freeDSP/freeDSP-aurora/SOURCES/WEBAPP/ESP32/testing/dsp.html

Channel 1 | Input | HP | LShlv | PEQ | PEQ | PEQ | PEQ | PEQ | PEQ | PEQ | PEQ | PEQ | PEQ | HShlv | LP | Phase | Delay | Gain | OUT 1
Channel 2 | Input | HP | LShlv | PEQ | PEQ | PEQ | PEQ | PEQ | PEQ | PEQ | PEQ | PEQ | PEQ | HShlv | LP | Phase | Delay | Gain | OUT 2
Channel 3 | Input | HP | LShlv | PEQ | PEQ | PEQ | PEQ | PEQ | PEQ | PEQ | PEQ | PEQ | PEQ | HShlv | LP | Phase | Delay | Gain | OUT 3
Channel 4 | Input | HP | LShlv | PEQ | PEQ | PEQ | PEQ | PEQ | PEQ | PEQ | PEQ | PEQ | PEQ | HShlv | LP | Phase | Delay | Gain | OUT 4
Channel 5 | Input | HP | LShlv | PEQ | PEQ | PEQ | PEQ | PEQ | PEQ | PEQ | PEQ | PEQ | PEQ | HShlv | LP | Phase | Delay | Gain | OUT 5
Channel 6 | Input | HP | LShlv | PEQ | PEQ | PEQ | PEQ | PEQ | PEQ | PEQ | PEQ | PEQ | PEQ | HShlv | LP | Phase | Delay | Gain | OUT 6
Channel 7 | Input | HP | LShlv | PEQ | PEQ | PEQ | PEQ | PEQ | PEQ | PEQ | PEQ | PEQ | PEQ | HShlv | LP | Phase | Delay | Gain | OUT 7
Channel 8 | Input | HP | LShlv | PEQ | PEQ | PEQ | PEQ | PEQ | PEQ | PEQ | PEQ | PEQ | PEQ | HShlv | LP | Phase | Delay | Gain | OUT 8

×

Input

Send

×

High Pass
| Hz
Send

×

Low Shelving
| dB
| Hz
| S
Send

×

Parametric EQ
| dB
| Hz
| Q
Send

×

High Shelving
| dB
| Hz
| S
Send

×

Low Pass
| Hz
Send

×

Phase
| Hz
| Q
Invert
Send

×

Delay
| ms
Send

×

Gain
| dB
Send
