freeDSP/freeDSP-aurora/ADDONS/AddOnA 1.0.0/KICAD/AddOnA.pdf

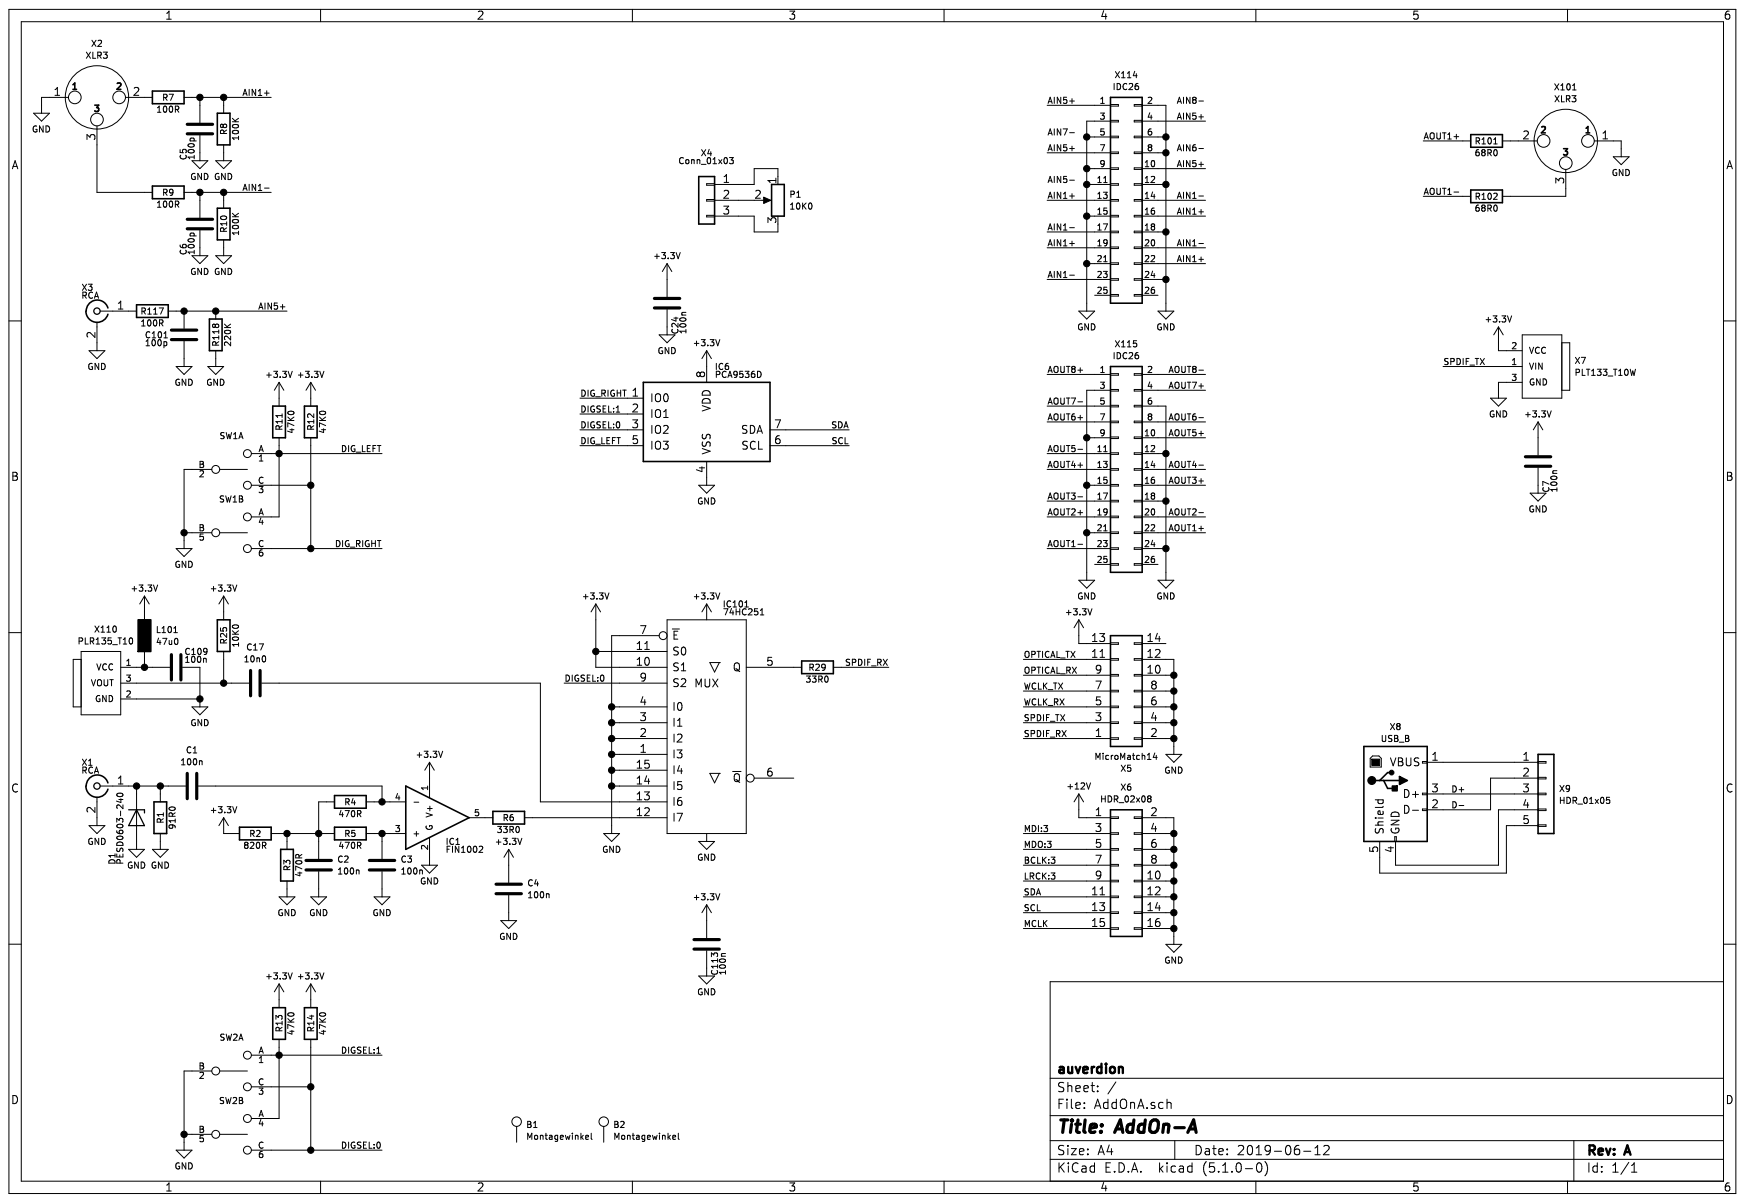
[picture p36: page 1]
