freeDSP/freeDSP-aurora/ADDONS/AddOnC/KICAD/AddOnC.pdf

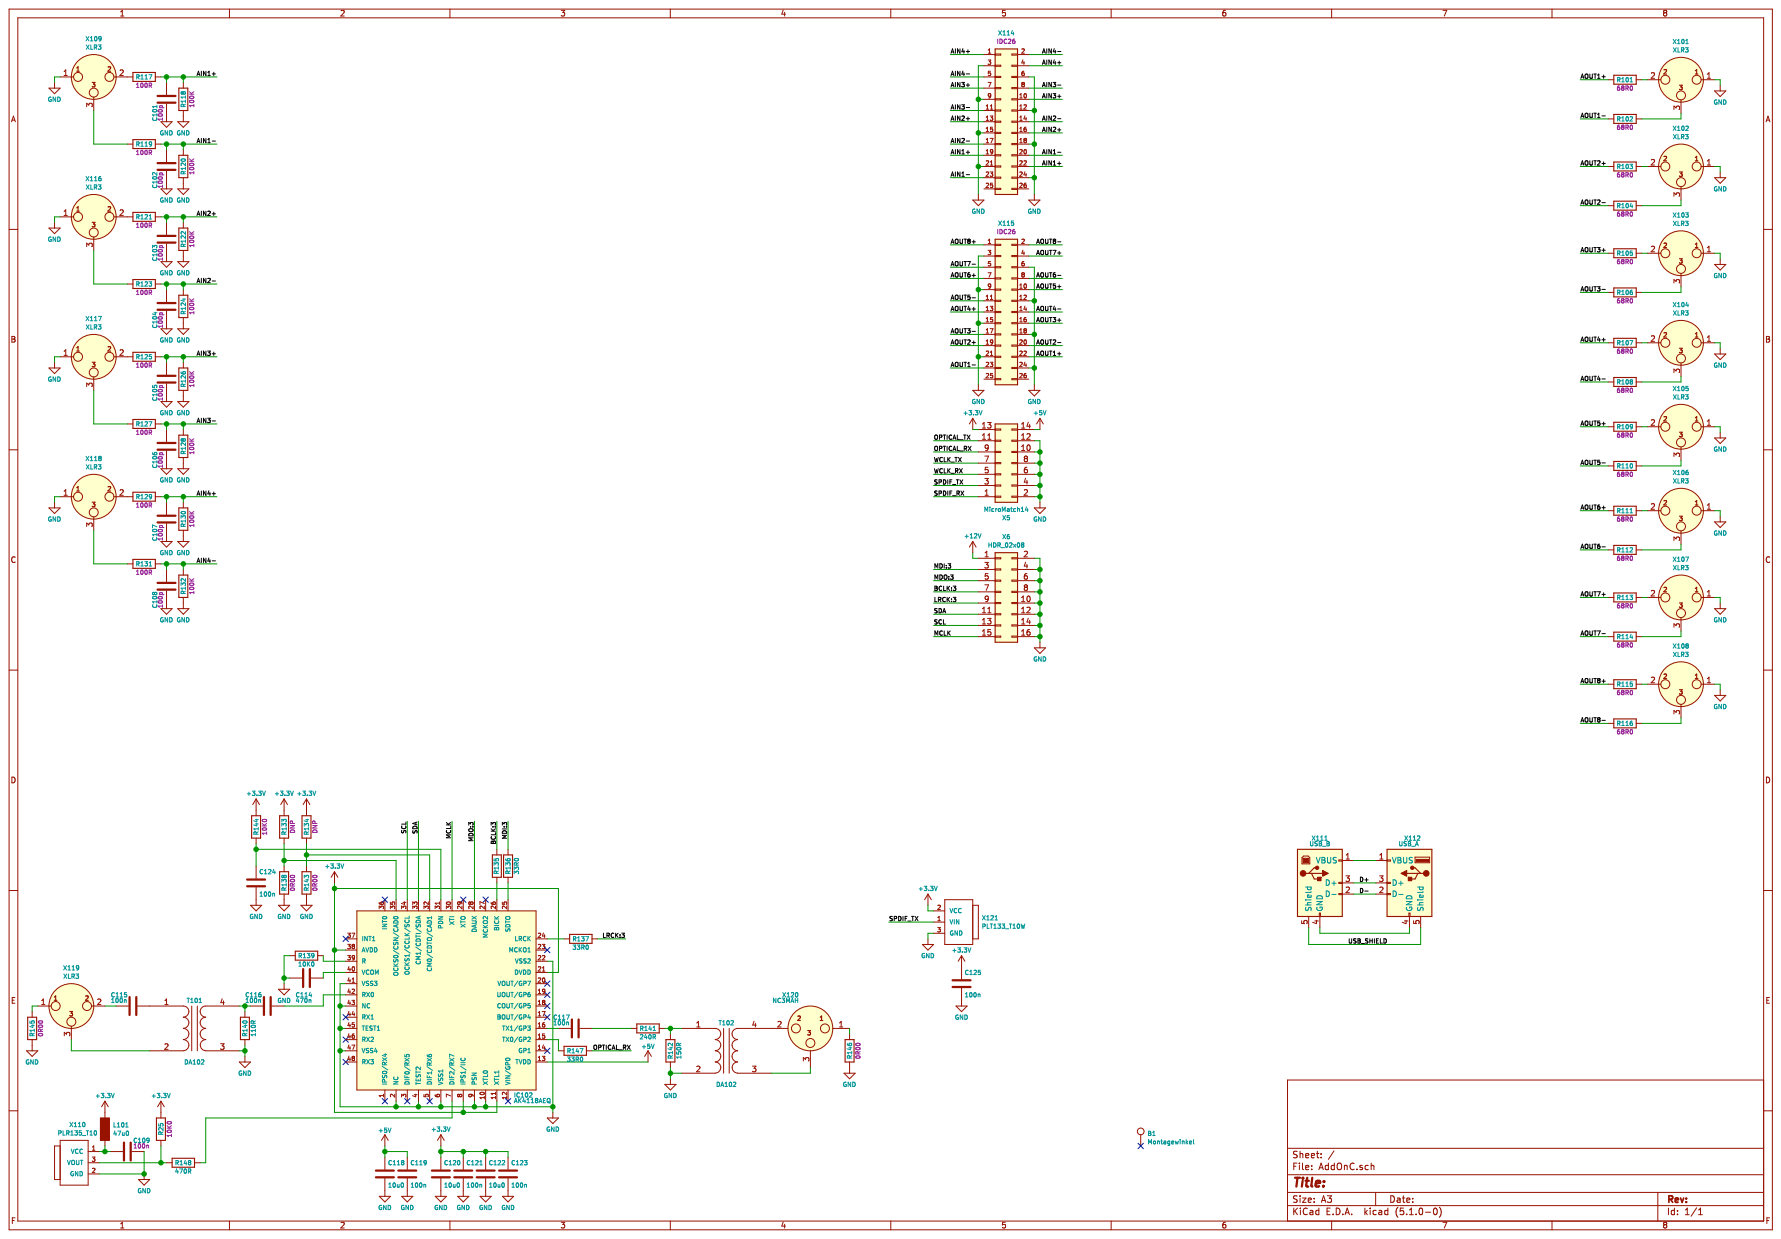
[picture p37: page 1]
