freeDSP/freeDSP-aurora/ADDONS/AddOnB/KICAD/Board A/AddOnB_BoardA.pdf

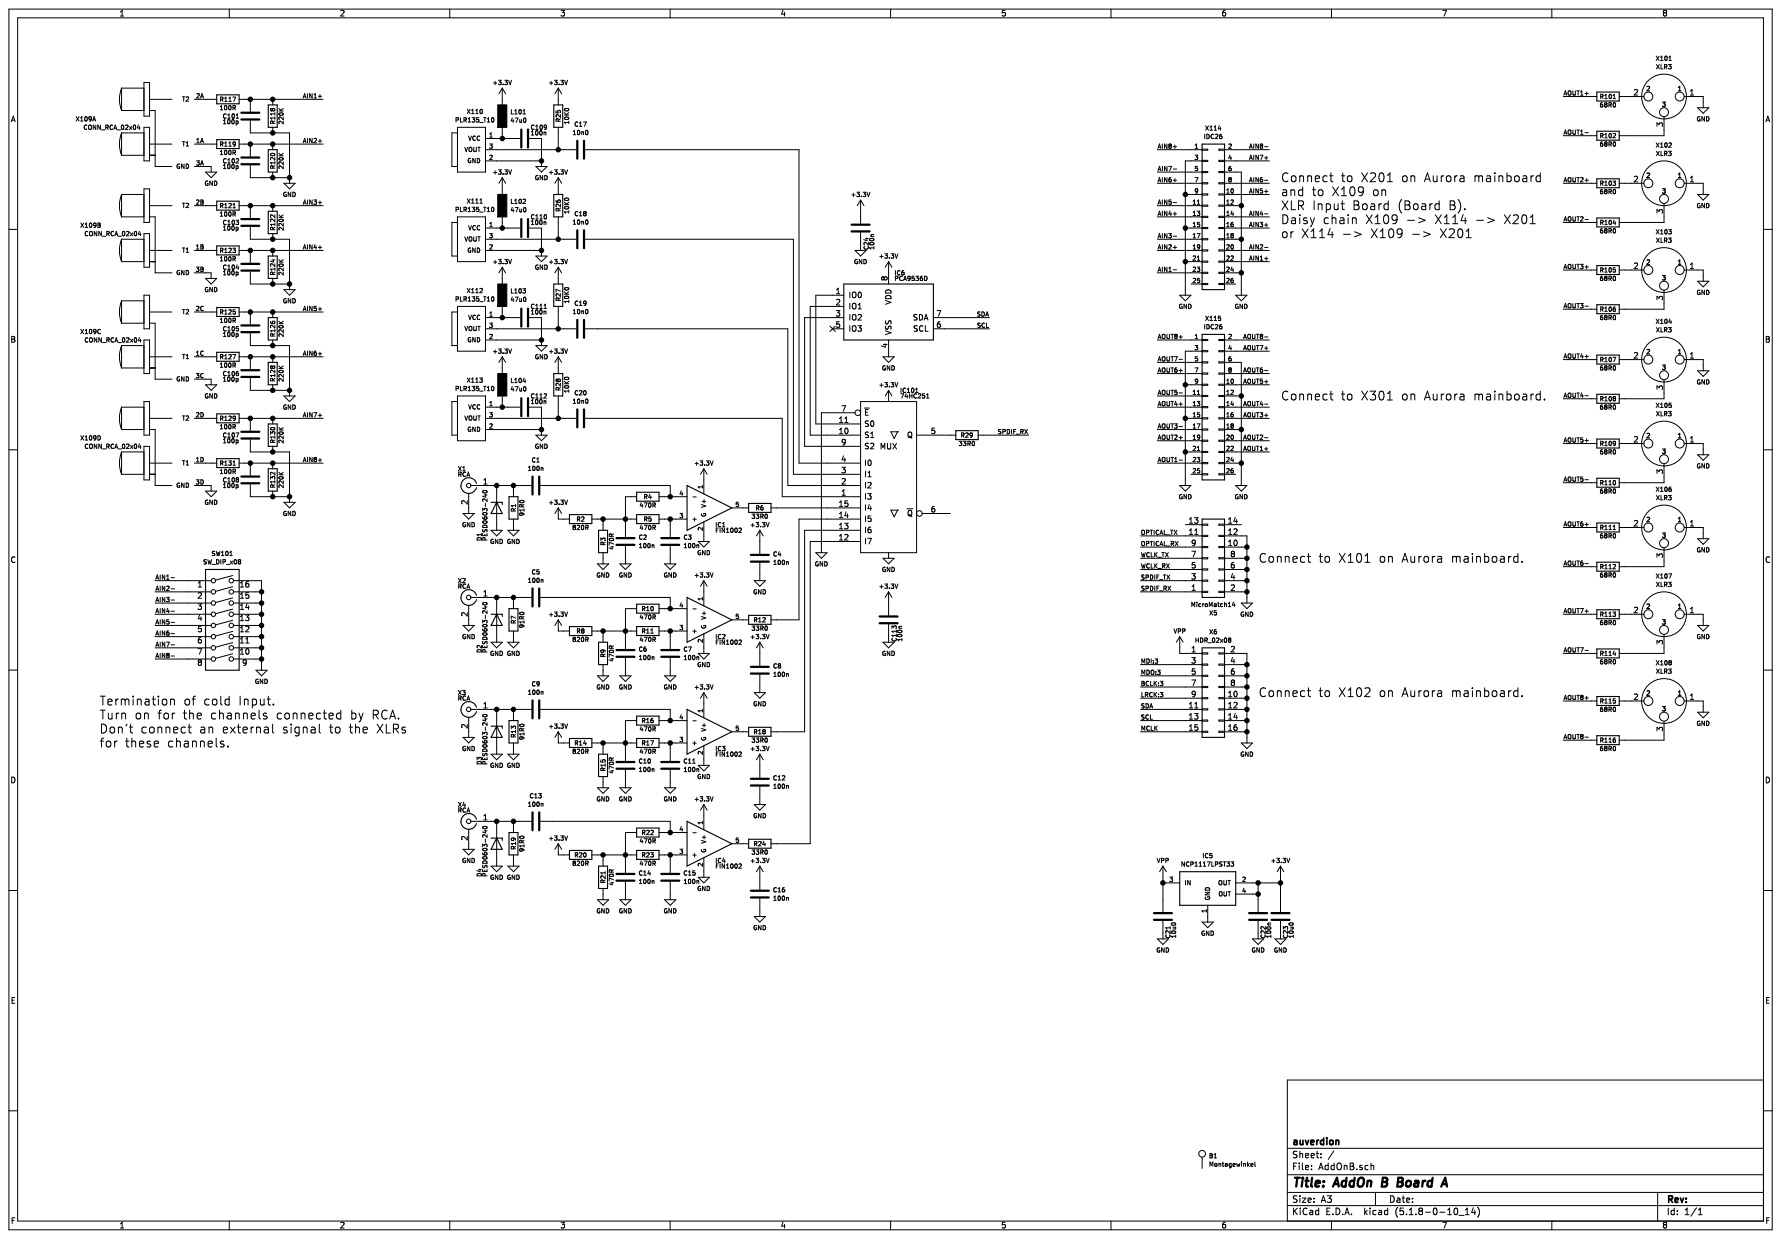
[picture p38: page 1]
