freeDSP/freeDSP-aurora/ADDONS/AddOnB/KICAD/Board B/AddOnB_BoardB.pdf

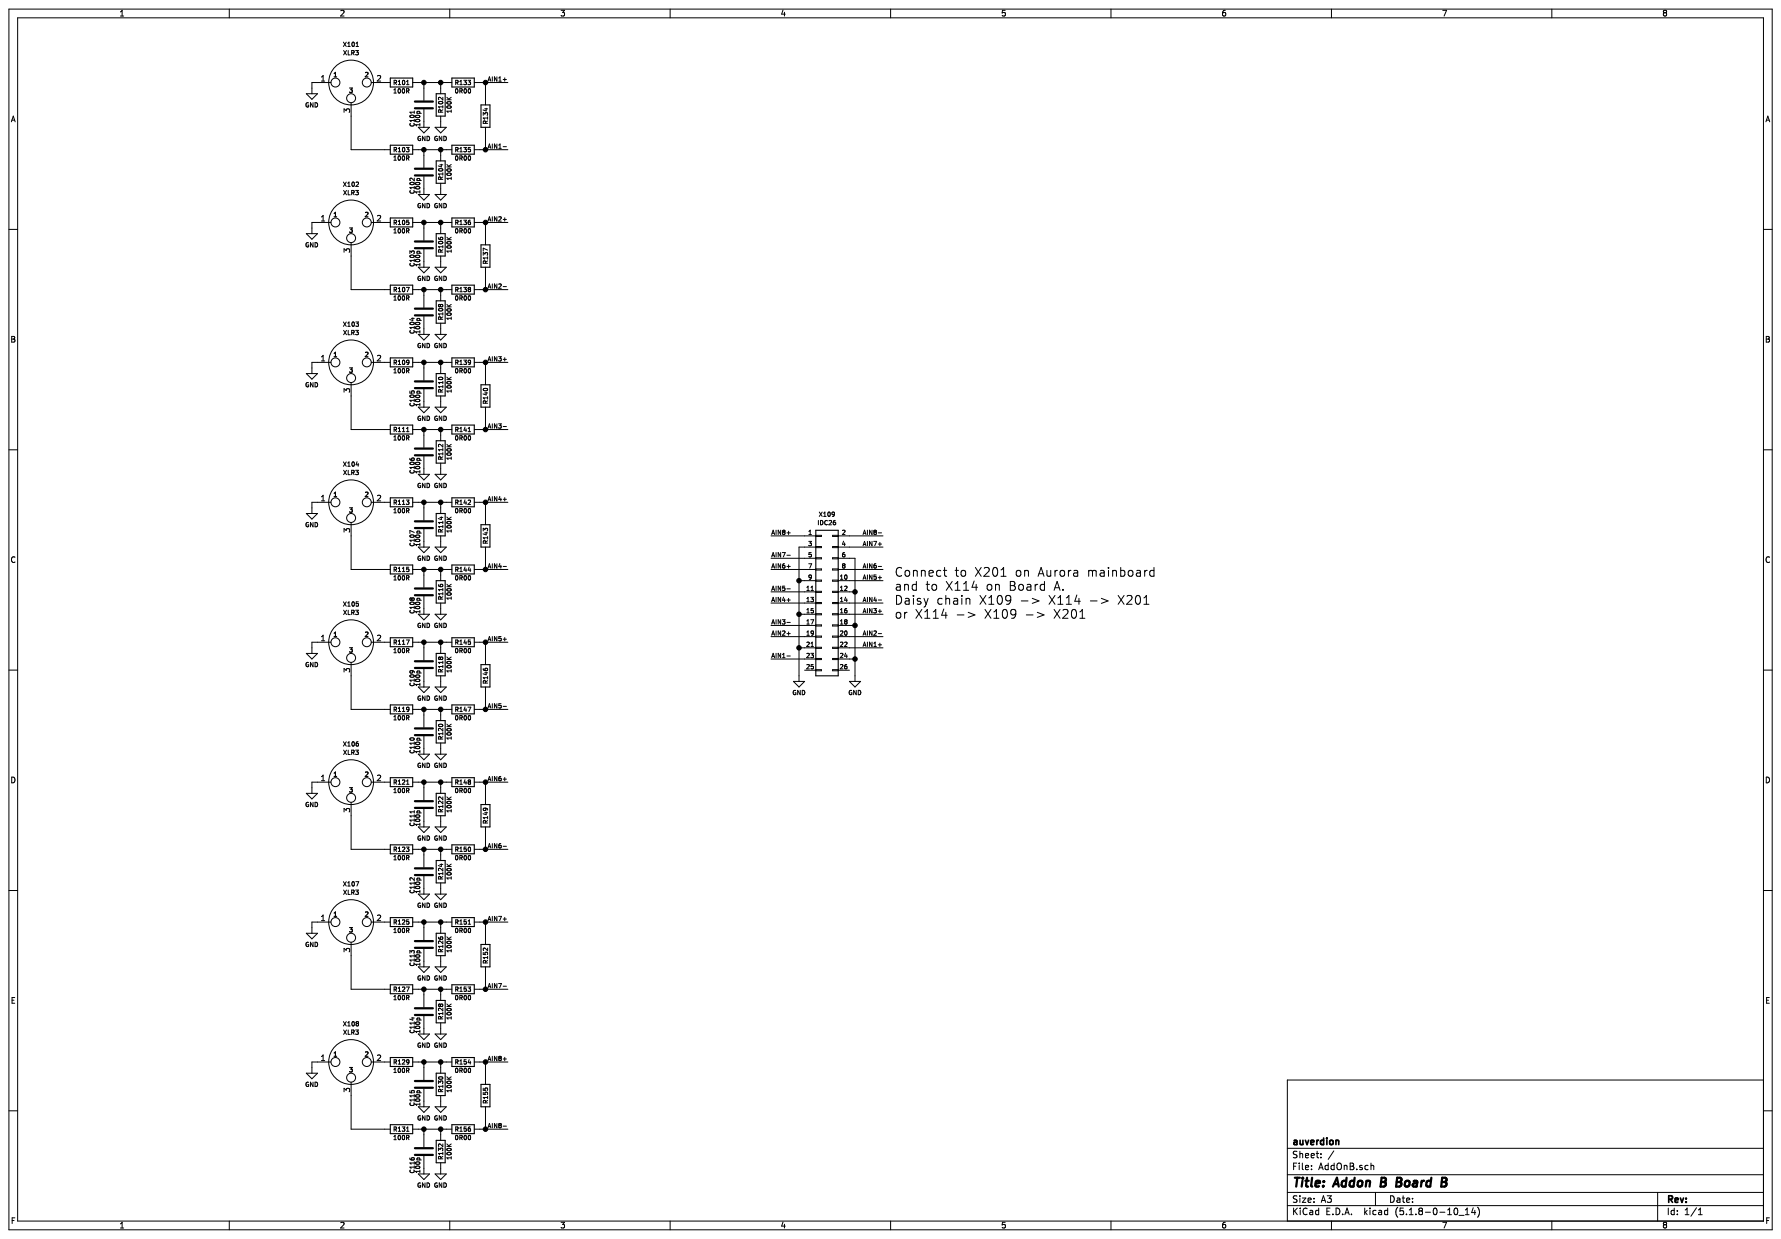
[picture p39: page 1]
