freeDSP/freeDSP-aurora/SOURCES/SIGMASTUDIO/4FIRs/4FIRs_IC_1_REG.h

/*
 * File:           C:\freeDSP-aurora\SOURCES\SIGMASTUDIO\4FIRs\4FIRs_IC_1_REG.h
 *
 * Created:        Sunday, March 13, 2022 8:20:32 PM
 * Description:    4FIRs:IC 1 control register definitions.
 *
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
 * This software may only be used to program products purchased from
 * Analog Devices for incorporation by you into audio products that
 * are intended for resale to audio product end users. This software
 * may not be distributed whole or in any part to third parties.
 *
 * Copyright ©2022 Analog Devices, Inc. All rights reserved.
 */
#ifndef __4FIRS_IC_1_REG_H__
#define __4FIRS_IC_1_REG_H__


/* PLL_CTRL0  - Registers (IC 1) */
#define REG_PLL_CTRL0_IC_1_ADDR                   0xF000
#define REG_PLL_CTRL0_IC_1_BYTE                   2
#define REG_PLL_CTRL0_IC_1_VALUE                  0x60

/* PLL_CTRL1  - Registers (IC 1) */
#define REG_PLL_CTRL1_IC_1_ADDR                   0xF001
#define REG_PLL_CTRL1_IC_1_BYTE                   2
#define REG_PLL_CTRL1_IC_1_VALUE                  0x3

/* PLL_CLK_SRC  - Registers (IC 1) */
#define REG_PLL_CLK_SRC_IC_1_ADDR                 0xF002
#define REG_PLL_CLK_SRC_IC_1_BYTE                 2
#define REG_PLL_CLK_SRC_IC_1_VALUE                0x1

/* PLL_ENABLE  - Registers (IC 1) */
#define REG_PLL_ENABLE_IC_1_ADDR                  0xF003
#define REG_PLL_ENABLE_IC_1_BYTE                  2
#define REG_PLL_ENABLE_IC_1_VALUE                 0x1

/* PLL_LOCK  - Registers (IC 1) */
#define REG_PLL_LOCK_IC_1_ADDR                    0xF004
#define REG_PLL_LOCK_IC_1_BYTE                    0
#define REG_PLL_LOCK_IC_1_VALUE                   0x1

/* MCLK_OUT  - Registers (IC 1) */
#define REG_MCLK_OUT_IC_1_ADDR                    0xF005
#define REG_MCLK_OUT_IC_1_BYTE                    2
#define REG_MCLK_OUT_IC_1_VALUE                   0x7

/* PLL_WATCHDOG  - Registers (IC 1) */
#define REG_PLL_WATCHDOG_IC_1_ADDR                0xF006
#define REG_PLL_WATCHDOG_IC_1_BYTE                2
#define REG_PLL_WATCHDOG_IC_1_VALUE               0x1

/* CLK_GEN1_M  - Registers (IC 1) */
#define REG_CLK_GEN1_M_IC_1_ADDR                  0xF020
#define REG_CLK_GEN1_M_IC_1_BYTE                  2
#define REG_CLK_GEN1_M_IC_1_VALUE                 0x6

/* CLK_GEN1_N  - Registers (IC 1) */
#define REG_CLK_GEN1_N_IC_1_ADDR                  0xF021
#define REG_CLK_GEN1_N_IC_1_BYTE                  2
#define REG_CLK_GEN1_N_IC_1_VALUE                 0x1

/* CLK_GEN2_M  - Registers (IC 1) */
#define REG_CLK_GEN2_M_IC_1_ADDR                  0xF022
#define REG_CLK_GEN2_M_IC_1_BYTE                  2
#define REG_CLK_GEN2_M_IC_1_VALUE                 0x9

/* CLK_GEN2_N  - Registers (IC 1) */
#define REG_CLK_GEN2_N_IC_1_ADDR                  0xF023
#define REG_CLK_GEN2_N_IC_1_BYTE                  2
#define REG_CLK_GEN2_N_IC_1_VALUE                 0x1

/* CLK_GEN3_M  - Registers (IC 1) */
#define REG_CLK_GEN3_M_IC_1_ADDR                  0xF024
#define REG_CLK_GEN3_M_IC_1_BYTE                  2
#define REG_CLK_GEN3_M_IC_1_VALUE                 0x0

/* CLK_GEN3_N  - Registers (IC 1) */
#define REG_CLK_GEN3_N_IC_1_ADDR                  0xF025
#define REG_CLK_GEN3_N_IC_1_BYTE                  2
#define REG_CLK_GEN3_N_IC_1_VALUE                 0x0

/* CLK_GEN3_SRC  - Registers (IC 1) */
#define REG_CLK_GEN3_SRC_IC_1_ADDR                0xF026
#define REG_CLK_GEN3_SRC_IC_1_BYTE                2
#define REG_CLK_GEN3_SRC_IC_1_VALUE               0xE

/* CLK_GEN3_LOCK  - Registers (IC 1) */
#define REG_CLK_GEN3_LOCK_IC_1_ADDR               0xF027
#define REG_CLK_GEN3_LOCK_IC_1_BYTE               0
#define REG_CLK_GEN3_LOCK_IC_1_VALUE              0x1

/* POWER_ENABLE0  - Registers (IC 1) */
#define REG_POWER_ENABLE0_IC_1_ADDR               0xF050
#define REG_POWER_ENABLE0_IC_1_BYTE               2
#define REG_POWER_ENABLE0_IC_1_VALUE              0x5FF

/* POWER_ENABLE1  - Registers (IC 1) */
#define REG_POWER_ENABLE1_IC_1_ADDR               0xF051
#define REG_POWER_ENABLE1_IC_1_BYTE               2
#define REG_POWER_ENABLE1_IC_1_VALUE              0x7

/* ASRC_INPUT0  - Registers (IC 1) */
#define REG_ASRC_INPUT0_IC_1_ADDR                 0xF100
#define REG_ASRC_INPUT0_IC_1_BYTE                 2
#define REG_ASRC_INPUT0_IC_1_VALUE                0x3

/* ASRC_INPUT1  - Registers (IC 1) */
#define REG_ASRC_INPUT1_IC_1_ADDR                 0xF101
#define REG_ASRC_INPUT1_IC_1_BYTE                 2
#define REG_ASRC_INPUT1_IC_1_VALUE                0x0

/* ASRC_INPUT2  - Registers (IC 1) */
#define REG_ASRC_INPUT2_IC_1_ADDR                 0xF102
#define REG_ASRC_INPUT2_IC_1_BYTE                 2
#define REG_ASRC_INPUT2_IC_1_VALUE                0x0

/* ASRC_INPUT3  - Registers (IC 1) */
#define REG_ASRC_INPUT3_IC_1_ADDR                 0xF103
#define REG_ASRC_INPUT3_IC_1_BYTE                 2
#define REG_ASRC_INPUT3_IC_1_VALUE                0x0

/* ASRC_INPUT4  - Registers (IC 1) */
#define REG_ASRC_INPUT4_IC_1_ADDR                 0xF104
#define REG_ASRC_INPUT4_IC_1_BYTE                 2
#define REG_ASRC_INPUT4_IC_1_VALUE                0x0

/* ASRC_INPUT5  - Registers (IC 1) */
#define REG_ASRC_INPUT5_IC_1_ADDR                 0xF105
#define REG_ASRC_INPUT5_IC_1_BYTE                 2
#define REG_ASRC_INPUT5_IC_1_VALUE                0x0

/* ASRC_INPUT6  - Registers (IC 1) */
#define REG_ASRC_INPUT6_IC_1_ADDR                 0xF106
#define REG_ASRC_INPUT6_IC_1_BYTE                 2
#define REG_ASRC_INPUT6_IC_1_VALUE                0x0

/* ASRC_INPUT7  - Registers (IC 1) */
#define REG_ASRC_INPUT7_IC_1_ADDR                 0xF107
#define REG_ASRC_INPUT7_IC_1_BYTE                 2
#define REG_ASRC_INPUT7_IC_1_VALUE                0x0

/* ASRC_OUT_RATE0  - Registers (IC 1) */
#define REG_ASRC_OUT_RATE0_IC_1_ADDR              0xF140
#define REG_ASRC_OUT_RATE0_IC_1_BYTE              2
#define REG_ASRC_OUT_RATE0_IC_1_VALUE             0x6

/* ASRC_OUT_RATE1  - Registers (IC 1) */
#define REG_ASRC_OUT_RATE1_IC_1_ADDR              0xF141
#define REG_ASRC_OUT_RATE1_IC_1_BYTE              2
#define REG_ASRC_OUT_RATE1_IC_1_VALUE             0x0

/* ASRC_OUT_RATE2  - Registers (IC 1) */
#define REG_ASRC_OUT_RATE2_IC_1_ADDR              0xF142
#define REG_ASRC_OUT_RATE2_IC_1_BYTE              2
#define REG_ASRC_OUT_RATE2_IC_1_VALUE             0x0

/* ASRC_OUT_RATE3  - Registers (IC 1) */
#define REG_ASRC_OUT_RATE3_IC_1_ADDR              0xF143
#define REG_ASRC_OUT_RATE3_IC_1_BYTE              2
#define REG_ASRC_OUT_RATE3_IC_1_VALUE             0x0

/* ASRC_OUT_RATE4  - Registers (IC 1) */
#define REG_ASRC_OUT_RATE4_IC_1_ADDR              0xF144
#define REG_ASRC_OUT_RATE4_IC_1_BYTE              2
#define REG_ASRC_OUT_RATE4_IC_1_VALUE             0x0

/* ASRC_OUT_RATE5  - Registers (IC 1) */
#define REG_ASRC_OUT_RATE5_IC_1_ADDR              0xF145
#define REG_ASRC_OUT_RATE5_IC_1_BYTE              2
#define REG_ASRC_OUT_RATE5_IC_1_VALUE             0x0

/* ASRC_OUT_RATE6  - Registers (IC 1) */
#define REG_ASRC_OUT_RATE6_IC_1_ADDR              0xF146
#define REG_ASRC_OUT_RATE6_IC_1_BYTE              2
#define REG_ASRC_OUT_RATE6_IC_1_VALUE             0x0

/* ASRC_OUT_RATE7  - Registers (IC 1) */
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
#define REG_SOUT_SOURCE18_IC_1_VALUE              0x0

/* SOUT_SOURCE19  - Registers (IC 1) */
#define REG_SOUT_SOURCE19_IC_1_ADDR               0xF193
#define REG_SOUT_SOURCE19_IC_1_BYTE               2
#define REG_SOUT_SOURCE19_IC_1_VALUE              0x0

/* SOUT_SOURCE20  - Registers (IC 1) */
#define REG_SOUT_SOURCE20_IC_1_ADDR               0xF194
#define REG_SOUT_SOURCE20_IC_1_BYTE               2
#define REG_SOUT_SOURCE20_IC_1_VALUE              0x0

/* SOUT_SOURCE21  - Registers (IC 1) */
#define REG_SOUT_SOURCE21_IC_1_ADDR               0xF195
#define REG_SOUT_SOURCE21_IC_1_BYTE               2
#define REG_SOUT_SOURCE21_IC_1_VALUE              0x0

/* SOUT_SOURCE22  - Registers (IC 1) */
#define REG_SOUT_SOURCE22_IC_1_ADDR               0xF196
#define REG_SOUT_SOURCE22_IC_1_BYTE               2
#define REG_SOUT_SOURCE22_IC_1_VALUE              0x0

/* SOUT_SOURCE23  - Registers (IC 1) */
#define REG_SOUT_SOURCE23_IC_1_ADDR               0xF197
#define REG_SOUT_SOURCE23_IC_1_BYTE               2
#define REG_SOUT_SOURCE23_IC_1_VALUE              0x0

/* SPDIFTX_INPUT  - Registers (IC 1) */
#define REG_SPDIFTX_INPUT_IC_1_ADDR               0xF1C0
#define REG_SPDIFTX_INPUT_IC_1_BYTE               2
#define REG_SPDIFTX_INPUT_IC_1_VALUE              0x1

/* SERIAL_BYTE_0_0  - Registers (IC 1) */
#define REG_SERIAL_BYTE_0_0_IC_1_ADDR             0xF200
#define REG_SERIAL_BYTE_0_0_IC_1_BYTE             2
#define REG_SERIAL_BYTE_0_0_IC_1_VALUE            0x93CA

/* SERIAL_BYTE_0_1  - Registers (IC 1) */
#define REG_SERIAL_BYTE_0_1_IC_1_ADDR             0xF201
#define REG_SERIAL_BYTE_0_1_IC_1_BYTE             2
#define REG_SERIAL_BYTE_0_1_IC_1_VALUE            0x2

/* SERIAL_BYTE_1_0  - Registers (IC 1) */
#define REG_SERIAL_BYTE_1_0_IC_1_ADDR             0xF204
#define REG_SERIAL_BYTE_1_0_IC_1_BYTE             2
#define REG_SERIAL_BYTE_1_0_IC_1_VALUE            0x260A

/* SERIAL_BYTE_1_1  - Registers (IC 1) */
#define REG_SERIAL_BYTE_1_1_IC_1_ADDR             0xF205
#define REG_SERIAL_BYTE_1_1_IC_1_BYTE             2
#define REG_SERIAL_BYTE_1_1_IC_1_VALUE            0x2

/* SERIAL_BYTE_2_0  - Registers (IC 1) */
#define REG_SERIAL_BYTE_2_0_IC_1_ADDR             0xF208
#define REG_SERIAL_BYTE_2_0_IC_1_BYTE             2
#define REG_SERIAL_BYTE_2_0_IC_1_VALUE            0x93CA

/* SERIAL_BYTE_2_1  - Registers (IC 1) */
#define REG_SERIAL_BYTE_2_1_IC_1_ADDR             0xF209
#define REG_SERIAL_BYTE_2_1_IC_1_BYTE             2
#define REG_SERIAL_BYTE_2_1_IC_1_VALUE            0x2

/* SERIAL_BYTE_3_0  - Registers (IC 1) */
#define REG_SERIAL_BYTE_3_0_IC_1_ADDR             0xF20C
#define REG_SERIAL_BYTE_3_0_IC_1_BYTE             2
#define REG_SERIAL_BYTE_3_0_IC_1_VALUE            0x6F80

/* SERIAL_BYTE_3_1  - Registers (IC 1) */
#define REG_SERIAL_BYTE_3_1_IC_1_ADDR             0xF20D
#define REG_SERIAL_BYTE_3_1_IC_1_BYTE             2
#define REG_SERIAL_BYTE_3_1_IC_1_VALUE            0x2

/* SERIAL_BYTE_4_0  - Registers (IC 1) */
#define REG_SERIAL_BYTE_4_0_IC_1_ADDR             0xF210
#define REG_SERIAL_BYTE_4_0_IC_1_BYTE             2
#define REG_SERIAL_BYTE_4_0_IC_1_VALUE            0x93CA

/* SERIAL_BYTE_4_1  - Registers (IC 1) */
#define REG_SERIAL_BYTE_4_1_IC_1_ADDR             0xF211
#define REG_SERIAL_BYTE_4_1_IC_1_BYTE             2
#define REG_SERIAL_BYTE_4_1_IC_1_VALUE            0x2

/* SERIAL_BYTE_5_0  - Registers (IC 1) */
#define REG_SERIAL_BYTE_5_0_IC_1_ADDR             0xF214
#define REG_SERIAL_BYTE_5_0_IC_1_BYTE             2
#define REG_SERIAL_BYTE_5_0_IC_1_VALUE            0x260A

/* SERIAL_BYTE_5_1  - Registers (IC 1) */
#define REG_SERIAL_BYTE_5_1_IC_1_ADDR             0xF215
#define REG_SERIAL_BYTE_5_1_IC_1_BYTE             2
#define REG_SERIAL_BYTE_5_1_IC_1_VALUE            0x2

/* SERIAL_BYTE_6_0  - Registers (IC 1) */
#define REG_SERIAL_BYTE_6_0_IC_1_ADDR             0xF218
#define REG_SERIAL_BYTE_6_0_IC_1_BYTE             2
#define REG_SERIAL_BYTE_6_0_IC_1_VALUE            0x0

/* SERIAL_BYTE_6_1  - Registers (IC 1) */
#define REG_SERIAL_BYTE_6_1_IC_1_ADDR             0xF219
#define REG_SERIAL_BYTE_6_1_IC_1_BYTE             2
#define REG_SERIAL_BYTE_6_1_IC_1_VALUE            0x2

/* SERIAL_BYTE_7_0  - Registers (IC 1) */
#define REG_SERIAL_BYTE_7_0_IC_1_ADDR             0xF21C
#define REG_SERIAL_BYTE_7_0_IC_1_BYTE             2
#define REG_SERIAL_BYTE_7_0_IC_1_VALUE            0x0

/* SERIAL_BYTE_7_1  - Registers (IC 1) */
#define REG_SERIAL_BYTE_7_1_IC_1_ADDR             0xF21D
#define REG_SERIAL_BYTE_7_1_IC_1_BYTE             2
#define REG_SERIAL_BYTE_7_1_IC_1_VALUE            0x2

/* FTDM_IN0  - Registers (IC 1) */
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
#define REG_FTDM_OUT57_IC_1_VALUE                 0x0

/* FTDM_OUT58  - Registers (IC 1) */
#define REG_FTDM_OUT58_IC_1_ADDR                  0xF3BA
#define REG_FTDM_OUT58_IC_1_BYTE                  2
#define REG_FTDM_OUT58_IC_1_VALUE                 0x0

/* FTDM_OUT59  - Registers (IC 1) */
#define REG_FTDM_OUT59_IC_1_ADDR                  0xF3BB
#define REG_FTDM_OUT59_IC_1_BYTE                  2
#define REG_FTDM_OUT59_IC_1_VALUE                 0x0

/* FTDM_OUT60  - Registers (IC 1) */
#define REG_FTDM_OUT60_IC_1_ADDR                  0xF3BC
#define REG_FTDM_OUT60_IC_1_BYTE                  2
#define REG_FTDM_OUT60_IC_1_VALUE                 0x0

/* FTDM_OUT61  - Registers (IC 1) */
#define REG_FTDM_OUT61_IC_1_ADDR                  0xF3BD
#define REG_FTDM_OUT61_IC_1_BYTE                  2
#define REG_FTDM_OUT61_IC_1_VALUE                 0x0

/* FTDM_OUT62  - Registers (IC 1) */
#define REG_FTDM_OUT62_IC_1_ADDR                  0xF3BE
#define REG_FTDM_OUT62_IC_1_BYTE                  2
#define REG_FTDM_OUT62_IC_1_VALUE                 0x0

/* FTDM_OUT63  - Registers (IC 1) */
#define REG_FTDM_OUT63_IC_1_ADDR                  0xF3BF
#define REG_FTDM_OUT63_IC_1_BYTE                  2
#define REG_FTDM_OUT63_IC_1_VALUE                 0x0

/* HIBERNATE  - Registers (IC 1) */
#define REG_HIBERNATE_IC_1_ADDR                   0xF400
#define REG_HIBERNATE_IC_1_BYTE                   2
#define REG_HIBERNATE_IC_1_VALUE                  0x0

/* START_PULSE  - Registers (IC 1) */
#define REG_START_PULSE_IC_1_ADDR                 0xF401
#define REG_START_PULSE_IC_1_BYTE                 2
#define REG_START_PULSE_IC_1_VALUE                0x2

/* START_CORE  - Registers (IC 1) */
#define REG_START_CORE_IC_1_ADDR                  0xF402
#define REG_START_CORE_IC_1_BYTE                  2
#define REG_START_CORE_IC_1_VALUE                 0x1

/* KILL_CORE  - Registers (IC 1) */
#define REG_KILL_CORE_IC_1_ADDR                   0xF403
#define REG_KILL_CORE_IC_1_BYTE                   2
#define REG_KILL_CORE_IC_1_VALUE                  0x0

/* START_ADDRESS  - Registers (IC 1) */
#define REG_START_ADDRESS_IC_1_ADDR               0xF404
#define REG_START_ADDRESS_IC_1_BYTE               2
#define REG_START_ADDRESS_IC_1_VALUE              0x0

/* CORE_STATUS  - Registers (IC 1) */
#define REG_CORE_STATUS_IC_1_ADDR                 0xF405
#define REG_CORE_STATUS_IC_1_BYTE                 0
#define REG_CORE_STATUS_IC_1_VALUE                0x1

/* DEBUG_MODE  - Registers (IC 1) */
#define REG_DEBUG_MODE_IC_1_ADDR                  0xF420
#define REG_DEBUG_MODE_IC_1_BYTE                  2
#define REG_DEBUG_MODE_IC_1_VALUE                 0x0

/* PANIC_CLEAR  - Registers (IC 1) */
#define REG_PANIC_CLEAR_IC_1_ADDR                 0xF421
#define REG_PANIC_CLEAR_IC_1_BYTE                 2
#define REG_PANIC_CLEAR_IC_1_VALUE                0x0

/* PANIC_PARITY_MASK  - Registers (IC 1) */
#define REG_PANIC_PARITY_MASK_IC_1_ADDR           0xF422
#define REG_PANIC_PARITY_MASK_IC_1_BYTE           2
#define REG_PANIC_PARITY_MASK_IC_1_VALUE          0x3

/* PANIC_SOFTWARE_MASK  - Registers (IC 1) */
#define REG_PANIC_SOFTWARE_MASK_IC_1_ADDR         0xF423
#define REG_PANIC_SOFTWARE_MASK_IC_1_BYTE         2
#define REG_PANIC_SOFTWARE_MASK_IC_1_VALUE        0x0

/* PANIC_WD_MASK  - Registers (IC 1) */
#define REG_PANIC_WD_MASK_IC_1_ADDR               0xF424
#define REG_PANIC_WD_MASK_IC_1_BYTE               2
#define REG_PANIC_WD_MASK_IC_1_VALUE              0x0

/* PANIC_STACK_MASK  - Registers (IC 1) */
#define REG_PANIC_STACK_MASK_IC_1_ADDR            0xF425
#define REG_PANIC_STACK_MASK_IC_1_BYTE            2
#define REG_PANIC_STACK_MASK_IC_1_VALUE           0x0

/* PANIC_LOOP_MASK  - Registers (IC 1) */
#define REG_PANIC_LOOP_MASK_IC_1_ADDR             0xF426
#define REG_PANIC_LOOP_MASK_IC_1_BYTE             2
#define REG_PANIC_LOOP_MASK_IC_1_VALUE            0x0

/* PANIC_FLAG  - Registers (IC 1) */
#define REG_PANIC_FLAG_IC_1_ADDR                  0xF427
#define REG_PANIC_FLAG_IC_1_BYTE                  0
#define REG_PANIC_FLAG_IC_1_VALUE                 0x1

/* PANIC_CODE  - Registers (IC 1) */
#define REG_PANIC_CODE_IC_1_ADDR                  0xF428
#define REG_PANIC_CODE_IC_1_BYTE                  0
#define REG_PANIC_CODE_IC_1_VALUE                 0x80

/* DECODE_OP0  - Registers (IC 1) */
#define REG_DECODE_OP0_IC_1_ADDR                  0xF429
#define REG_DECODE_OP0_IC_1_BYTE                  0
#define REG_DECODE_OP0_IC_1_VALUE                 0x0

/* DECODE_OP1  - Registers (IC 1) */
#define REG_DECODE_OP1_IC_1_ADDR                  0xF42A
#define REG_DECODE_OP1_IC_1_BYTE                  0
#define REG_DECODE_OP1_IC_1_VALUE                 0x0

/* DECODE_OP2  - Registers (IC 1) */
#define REG_DECODE_OP2_IC_1_ADDR                  0xF42B
#define REG_DECODE_OP2_IC_1_BYTE                  0
#define REG_DECODE_OP2_IC_1_VALUE                 0xFFA8

/* DECODE_OP3  - Registers (IC 1) */
#define REG_DECODE_OP3_IC_1_ADDR                  0xF42C
#define REG_DECODE_OP3_IC_1_BYTE                  0
#define REG_DECODE_OP3_IC_1_VALUE                 0xA40

/* EXECUTE_OP0  - Registers (IC 1) */
#define REG_EXECUTE_OP0_IC_1_ADDR                 0xF42D
#define REG_EXECUTE_OP0_IC_1_BYTE                 0
#define REG_EXECUTE_OP0_IC_1_VALUE                0x0

/* EXECUTE_OP1  - Registers (IC 1) */
#define REG_EXECUTE_OP1_IC_1_ADDR                 0xF42E
#define REG_EXECUTE_OP1_IC_1_BYTE                 0
#define REG_EXECUTE_OP1_IC_1_VALUE                0x0

/* EXECUTE_OP2  - Registers (IC 1) */
#define REG_EXECUTE_OP2_IC_1_ADDR                 0xF42F
#define REG_EXECUTE_OP2_IC_1_BYTE                 0
#define REG_EXECUTE_OP2_IC_1_VALUE                0x0

/* EXECUTE_OP3  - Registers (IC 1) */
#define REG_EXECUTE_OP3_IC_1_ADDR                 0xF430
#define REG_EXECUTE_OP3_IC_1_BYTE                 0
#define REG_EXECUTE_OP3_IC_1_VALUE                0x0

/* DECODE_COUNT  - Registers (IC 1) */
#define REG_DECODE_COUNT_IC_1_ADDR                0xF431
#define REG_DECODE_COUNT_IC_1_BYTE                0
#define REG_DECODE_COUNT_IC_1_VALUE               0xC0FF

/* EXECUTE_COUNT  - Registers (IC 1) */
#define REG_EXECUTE_COUNT_IC_1_ADDR               0xF432
#define REG_EXECUTE_COUNT_IC_1_BYTE               0
#define REG_EXECUTE_COUNT_IC_1_VALUE              0x0

/* SOFTWARE_VALUE_0  - Registers (IC 1) */
#define REG_SOFTWARE_VALUE_0_IC_1_ADDR            0xF433
#define REG_SOFTWARE_VALUE_0_IC_1_BYTE            0
#define REG_SOFTWARE_VALUE_0_IC_1_VALUE           0x0

/* SOFTWARE_VALUE_1  - Registers (IC 1) */
#define REG_SOFTWARE_VALUE_1_IC_1_ADDR            0xF434
#define REG_SOFTWARE_VALUE_1_IC_1_BYTE            0
#define REG_SOFTWARE_VALUE_1_IC_1_VALUE           0x0

/* WATCHDOG_MAXCOUNT  - Registers (IC 1) */
#define REG_WATCHDOG_MAXCOUNT_IC_1_ADDR           0xF443
#define REG_WATCHDOG_MAXCOUNT_IC_1_BYTE           2
#define REG_WATCHDOG_MAXCOUNT_IC_1_VALUE          0x0

/* WATCHDOG_PRESCALE  - Registers (IC 1) */
#define REG_WATCHDOG_PRESCALE_IC_1_ADDR           0xF444
#define REG_WATCHDOG_PRESCALE_IC_1_BYTE           2
#define REG_WATCHDOG_PRESCALE_IC_1_VALUE          0x0

/* BLOCKINT_EN  - Registers (IC 1) */
#define REG_BLOCKINT_EN_IC_1_ADDR                 0xF450
#define REG_BLOCKINT_EN_IC_1_BYTE                 2
#define REG_BLOCKINT_EN_IC_1_VALUE                0x0

/* BLOCKINT_VALUE  - Registers (IC 1) */
#define REG_BLOCKINT_VALUE_IC_1_ADDR              0xF451
#define REG_BLOCKINT_VALUE_IC_1_BYTE              2
#define REG_BLOCKINT_VALUE_IC_1_VALUE             0x0

/* PROG_CNTR0  - Registers (IC 1) */
#define REG_PROG_CNTR0_IC_1_ADDR                  0xF460
#define REG_PROG_CNTR0_IC_1_BYTE                  0
#define REG_PROG_CNTR0_IC_1_VALUE                 0x0

/* PROG_CNTR1  - Registers (IC 1) */
#define REG_PROG_CNTR1_IC_1_ADDR                  0xF461
#define REG_PROG_CNTR1_IC_1_BYTE                  0
#define REG_PROG_CNTR1_IC_1_VALUE                 0x86C

/* PROG_CNTR_CLEAR  - Registers (IC 1) */
#define REG_PROG_CNTR_CLEAR_IC_1_ADDR             0xF462
#define REG_PROG_CNTR_CLEAR_IC_1_BYTE             2
#define REG_PROG_CNTR_CLEAR_IC_1_VALUE            0x0

/* PROG_CNTR_LENGTH0  - Registers (IC 1) */
#define REG_PROG_CNTR_LENGTH0_IC_1_ADDR           0xF463
#define REG_PROG_CNTR_LENGTH0_IC_1_BYTE           0
#define REG_PROG_CNTR_LENGTH0_IC_1_VALUE          0x0

/* PROG_CNTR_LENGTH1  - Registers (IC 1) */
#define REG_PROG_CNTR_LENGTH1_IC_1_ADDR           0xF464
#define REG_PROG_CNTR_LENGTH1_IC_1_BYTE           0
#define REG_PROG_CNTR_LENGTH1_IC_1_VALUE          0x66A

/* PROG_CNTR_MAXLENGTH0  - Registers (IC 1) */
#define REG_PROG_CNTR_MAXLENGTH0_IC_1_ADDR        0xF465
#define REG_PROG_CNTR_MAXLENGTH0_IC_1_BYTE        0
#define REG_PROG_CNTR_MAXLENGTH0_IC_1_VALUE       0x0

/* PROG_CNTR_MAXLENGTH1  - Registers (IC 1) */
#define REG_PROG_CNTR_MAXLENGTH1_IC_1_ADDR        0xF466
#define REG_PROG_CNTR_MAXLENGTH1_IC_1_BYTE        0
#define REG_PROG_CNTR_MAXLENGTH1_IC_1_VALUE       0x120A

/* MP0_MODE  - Registers (IC 1) */
#define REG_MP0_MODE_IC_1_ADDR                    0xF510
#define REG_MP0_MODE_IC_1_BYTE                    2
#define REG_MP0_MODE_IC_1_VALUE                   0xD

/* MP1_MODE  - Registers (IC 1) */
#define REG_MP1_MODE_IC_1_ADDR                    0xF511
#define REG_MP1_MODE_IC_1_BYTE                    2
#define REG_MP1_MODE_IC_1_VALUE                   0x0

/* MP2_MODE  - Registers (IC 1) */
#define REG_MP2_MODE_IC_1_ADDR                    0xF512
#define REG_MP2_MODE_IC_1_BYTE                    2
#define REG_MP2_MODE_IC_1_VALUE                   0x0

/* MP3_MODE  - Registers (IC 1) */
#define REG_MP3_MODE_IC_1_ADDR                    0xF513
#define REG_MP3_MODE_IC_1_BYTE                    2
#define REG_MP3_MODE_IC_1_VALUE                   0x0

/* MP4_MODE  - Registers (IC 1) */
#define REG_MP4_MODE_IC_1_ADDR                    0xF514
#define REG_MP4_MODE_IC_1_BYTE                    2
#define REG_MP4_MODE_IC_1_VALUE                   0x0

/* MP5_MODE  - Registers (IC 1) */
#define REG_MP5_MODE_IC_1_ADDR                    0xF515
#define REG_MP5_MODE_IC_1_BYTE                    2
#define REG_MP5_MODE_IC_1_VALUE                   0x0

/* MP6_MODE  - Registers (IC 1) */
#define REG_MP6_MODE_IC_1_ADDR                    0xF516
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
#define REG_MP12_READ_IC_1_VALUE                  0x0

/* MP13_READ  - Registers (IC 1) */
#define REG_MP13_READ_IC_1_ADDR                   0xF53D
#define REG_MP13_READ_IC_1_BYTE                   0
#define REG_MP13_READ_IC_1_VALUE                  0x0

/* DMIC_CTRL0  - Registers (IC 1) */
#define REG_DMIC_CTRL0_IC_1_ADDR                  0xF560
#define REG_DMIC_CTRL0_IC_1_BYTE                  2
#define REG_DMIC_CTRL0_IC_1_VALUE                 0x4000

/* DMIC_CTRL1  - Registers (IC 1) */
#define REG_DMIC_CTRL1_IC_1_ADDR                  0xF561
#define REG_DMIC_CTRL1_IC_1_BYTE                  2
#define REG_DMIC_CTRL1_IC_1_VALUE                 0x4000

/* ASRC_LOCK  - Registers (IC 1) */
#define REG_ASRC_LOCK_IC_1_ADDR                   0xF580
#define REG_ASRC_LOCK_IC_1_BYTE                   0
#define REG_ASRC_LOCK_IC_1_VALUE                  0x1

/* ASRC_MUTE  - Registers (IC 1) */
#define REG_ASRC_MUTE_IC_1_ADDR                   0xF581
#define REG_ASRC_MUTE_IC_1_BYTE                   2
#define REG_ASRC_MUTE_IC_1_VALUE                  0x0

/* ASRC0_RATIO  - Registers (IC 1) */
#define REG_ASRC0_RATIO_IC_1_ADDR                 0xF582
#define REG_ASRC0_RATIO_IC_1_BYTE                 0
#define REG_ASRC0_RATIO_IC_1_VALUE                0x1000

/* ASRC1_RATIO  - Registers (IC 1) */
#define REG_ASRC1_RATIO_IC_1_ADDR                 0xF583
#define REG_ASRC1_RATIO_IC_1_BYTE                 0
#define REG_ASRC1_RATIO_IC_1_VALUE                0x0

/* ASRC2_RATIO  - Registers (IC 1) */
#define REG_ASRC2_RATIO_IC_1_ADDR                 0xF584
#define REG_ASRC2_RATIO_IC_1_BYTE                 0
#define REG_ASRC2_RATIO_IC_1_VALUE                0x0

/* ASRC3_RATIO  - Registers (IC 1) */
#define REG_ASRC3_RATIO_IC_1_ADDR                 0xF585
#define REG_ASRC3_RATIO_IC_1_BYTE                 0
#define REG_ASRC3_RATIO_IC_1_VALUE                0x0

/* ASRC4_RATIO  - Registers (IC 1) */
#define REG_ASRC4_RATIO_IC_1_ADDR                 0xF586
#define REG_ASRC4_RATIO_IC_1_BYTE                 0
#define REG_ASRC4_RATIO_IC_1_VALUE                0x0

/* ASRC5_RATIO  - Registers (IC 1) */
#define REG_ASRC5_RATIO_IC_1_ADDR                 0xF587
#define REG_ASRC5_RATIO_IC_1_BYTE                 0
#define REG_ASRC5_RATIO_IC_1_VALUE                0x0

/* ASRC6_RATIO  - Registers (IC 1) */
#define REG_ASRC6_RATIO_IC_1_ADDR                 0xF588
#define REG_ASRC6_RATIO_IC_1_BYTE                 0
#define REG_ASRC6_RATIO_IC_1_VALUE                0x0

/* ASRC7_RATIO  - Registers (IC 1) */
#define REG_ASRC7_RATIO_IC_1_ADDR                 0xF589
#define REG_ASRC7_RATIO_IC_1_BYTE                 0
#define REG_ASRC7_RATIO_IC_1_VALUE                0x0

/* ADC_READ0  - Registers (IC 1) */
#define REG_ADC_READ0_IC_1_ADDR                   0xF5A0
#define REG_ADC_READ0_IC_1_BYTE                   0
#define REG_ADC_READ0_IC_1_VALUE                  0x26

/* ADC_READ1  - Registers (IC 1) */
#define REG_ADC_READ1_IC_1_ADDR                   0xF5A1
#define REG_ADC_READ1_IC_1_BYTE                   0
#define REG_ADC_READ1_IC_1_VALUE                  0x39

/* ADC_READ2  - Registers (IC 1) */
#define REG_ADC_READ2_IC_1_ADDR                   0xF5A2
#define REG_ADC_READ2_IC_1_BYTE                   0
#define REG_ADC_READ2_IC_1_VALUE                  0xEA

/* ADC_READ3  - Registers (IC 1) */
#define REG_ADC_READ3_IC_1_ADDR                   0xF5A3
#define REG_ADC_READ3_IC_1_BYTE                   0
#define REG_ADC_READ3_IC_1_VALUE                  0xBC

/* ADC_READ4  - Registers (IC 1) */
#define REG_ADC_READ4_IC_1_ADDR                   0xF5A4
#define REG_ADC_READ4_IC_1_BYTE                   0
#define REG_ADC_READ4_IC_1_VALUE                  0x11D

/* ADC_READ5  - Registers (IC 1) */
#define REG_ADC_READ5_IC_1_ADDR                   0xF5A5
#define REG_ADC_READ5_IC_1_BYTE                   0
#define REG_ADC_READ5_IC_1_VALUE                  0xE9

/* SPDIF_LOCK_DET  - Registers (IC 1) */
#define REG_SPDIF_LOCK_DET_IC_1_ADDR              0xF600
#define REG_SPDIF_LOCK_DET_IC_1_BYTE              0
#define REG_SPDIF_LOCK_DET_IC_1_VALUE             0x1

/* SPDIF_RX_CTRL  - Registers (IC 1) */
#define REG_SPDIF_RX_CTRL_IC_1_ADDR               0xF601
#define REG_SPDIF_RX_CTRL_IC_1_BYTE               2
#define REG_SPDIF_RX_CTRL_IC_1_VALUE              0x3

/* SPDIF_RX_DECODE  - Registers (IC 1) */
#define REG_SPDIF_RX_DECODE_IC_1_ADDR             0xF602
#define REG_SPDIF_RX_DECODE_IC_1_BYTE             0
#define REG_SPDIF_RX_DECODE_IC_1_VALUE            0x2EC

/* SPDIF_RX_COMPRMODE  - Registers (IC 1) */
#define REG_SPDIF_RX_COMPRMODE_IC_1_ADDR          0xF603
#define REG_SPDIF_RX_COMPRMODE_IC_1_BYTE          0
#define REG_SPDIF_RX_COMPRMODE_IC_1_VALUE         0x0

/* SPDIF_RESTART  - Registers (IC 1) */
#define REG_SPDIF_RESTART_IC_1_ADDR               0xF604
#define REG_SPDIF_RESTART_IC_1_BYTE               2
#define REG_SPDIF_RESTART_IC_1_VALUE              0x1

/* SPDIF_LOSS_OF_LOCK  - Registers (IC 1) */
#define REG_SPDIF_LOSS_OF_LOCK_IC_1_ADDR          0xF605
#define REG_SPDIF_LOSS_OF_LOCK_IC_1_BYTE          0
#define REG_SPDIF_LOSS_OF_LOCK_IC_1_VALUE         0x0

/* SPDIF_AUX_EN  - Registers (IC 1) */
#define REG_SPDIF_AUX_EN_IC_1_ADDR                0xF608
#define REG_SPDIF_AUX_EN_IC_1_BYTE                2
#define REG_SPDIF_AUX_EN_IC_1_VALUE               0x0

/* SPDIF_RX_AUXBIT_READY  - Registers (IC 1) */
#define REG_SPDIF_RX_AUXBIT_READY_IC_1_ADDR       0xF60F
#define REG_SPDIF_RX_AUXBIT_READY_IC_1_BYTE       0
#define REG_SPDIF_RX_AUXBIT_READY_IC_1_VALUE      0x1

/* SPDIF_RX_CS_LEFT_0  - Registers (IC 1) */
#define REG_SPDIF_RX_CS_LEFT_0_IC_1_ADDR          0xF610
#define REG_SPDIF_RX_CS_LEFT_0_IC_1_BYTE          0
#define REG_SPDIF_RX_CS_LEFT_0_IC_1_VALUE         0x0

/* SPDIF_RX_CS_LEFT_1  - Registers (IC 1) */
#define REG_SPDIF_RX_CS_LEFT_1_IC_1_ADDR          0xF611
#define REG_SPDIF_RX_CS_LEFT_1_IC_1_BYTE          0
#define REG_SPDIF_RX_CS_LEFT_1_IC_1_VALUE         0x0

/* SPDIF_RX_CS_LEFT_2  - Registers (IC 1) */
#define REG_SPDIF_RX_CS_LEFT_2_IC_1_ADDR          0xF612
#define REG_SPDIF_RX_CS_LEFT_2_IC_1_BYTE          0
#define REG_SPDIF_RX_CS_LEFT_2_IC_1_VALUE         0x0

/* SPDIF_RX_CS_LEFT_3  - Registers (IC 1) */
#define REG_SPDIF_RX_CS_LEFT_3_IC_1_ADDR          0xF613
#define REG_SPDIF_RX_CS_LEFT_3_IC_1_BYTE          0
#define REG_SPDIF_RX_CS_LEFT_3_IC_1_VALUE         0x0

/* SPDIF_RX_CS_LEFT_4  - Registers (IC 1) */
#define REG_SPDIF_RX_CS_LEFT_4_IC_1_ADDR          0xF614
#define REG_SPDIF_RX_CS_LEFT_4_IC_1_BYTE          0
#define REG_SPDIF_RX_CS_LEFT_4_IC_1_VALUE         0x0

/* SPDIF_RX_CS_LEFT_5  - Registers (IC 1) */
#define REG_SPDIF_RX_CS_LEFT_5_IC_1_ADDR          0xF615
#define REG_SPDIF_RX_CS_LEFT_5_IC_1_BYTE          0
#define REG_SPDIF_RX_CS_LEFT_5_IC_1_VALUE         0x0

/* SPDIF_RX_CS_LEFT_6  - Registers (IC 1) */
#define REG_SPDIF_RX_CS_LEFT_6_IC_1_ADDR          0xF616
#define REG_SPDIF_RX_CS_LEFT_6_IC_1_BYTE          0
#define REG_SPDIF_RX_CS_LEFT_6_IC_1_VALUE         0x0

/* SPDIF_RX_CS_LEFT_7  - Registers (IC 1) */
#define REG_SPDIF_RX_CS_LEFT_7_IC_1_ADDR          0xF617
#define REG_SPDIF_RX_CS_LEFT_7_IC_1_BYTE          0
#define REG_SPDIF_RX_CS_LEFT_7_IC_1_VALUE         0x0

/* SPDIF_RX_CS_LEFT_8  - Registers (IC 1) */
#define REG_SPDIF_RX_CS_LEFT_8_IC_1_ADDR          0xF618
#define REG_SPDIF_RX_CS_LEFT_8_IC_1_BYTE          0
#define REG_SPDIF_RX_CS_LEFT_8_IC_1_VALUE         0x0

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
#define REG_SPDIF_RX_PB_RIGHT_0_IC_1_VALUE        0x0

/* SPDIF_RX_PB_RIGHT_1  - Registers (IC 1) */
#define REG_SPDIF_RX_PB_RIGHT_1_IC_1_ADDR         0xF681
#define REG_SPDIF_RX_PB_RIGHT_1_IC_1_BYTE         0
#define REG_SPDIF_RX_PB_RIGHT_1_IC_1_VALUE        0x0

/* SPDIF_RX_PB_RIGHT_2  - Registers (IC 1) */
#define REG_SPDIF_RX_PB_RIGHT_2_IC_1_ADDR         0xF682
#define REG_SPDIF_RX_PB_RIGHT_2_IC_1_BYTE         0
#define REG_SPDIF_RX_PB_RIGHT_2_IC_1_VALUE        0x0

/* SPDIF_RX_PB_RIGHT_3  - Registers (IC 1) */
#define REG_SPDIF_RX_PB_RIGHT_3_IC_1_ADDR         0xF683
#define REG_SPDIF_RX_PB_RIGHT_3_IC_1_BYTE         0
#define REG_SPDIF_RX_PB_RIGHT_3_IC_1_VALUE        0x0

/* SPDIF_RX_PB_RIGHT_4  - Registers (IC 1) */
#define REG_SPDIF_RX_PB_RIGHT_4_IC_1_ADDR         0xF684
#define REG_SPDIF_RX_PB_RIGHT_4_IC_1_BYTE         0
#define REG_SPDIF_RX_PB_RIGHT_4_IC_1_VALUE        0x0

/* SPDIF_RX_PB_RIGHT_5  - Registers (IC 1) */
#define REG_SPDIF_RX_PB_RIGHT_5_IC_1_ADDR         0xF685
#define REG_SPDIF_RX_PB_RIGHT_5_IC_1_BYTE         0
#define REG_SPDIF_RX_PB_RIGHT_5_IC_1_VALUE        0x0

/* SPDIF_RX_PB_RIGHT_6  - Registers (IC 1) */
#define REG_SPDIF_RX_PB_RIGHT_6_IC_1_ADDR         0xF686
#define REG_SPDIF_RX_PB_RIGHT_6_IC_1_BYTE         0
#define REG_SPDIF_RX_PB_RIGHT_6_IC_1_VALUE        0x0

/* SPDIF_RX_PB_RIGHT_7  - Registers (IC 1) */
#define REG_SPDIF_RX_PB_RIGHT_7_IC_1_ADDR         0xF687
#define REG_SPDIF_RX_PB_RIGHT_7_IC_1_BYTE         0
#define REG_SPDIF_RX_PB_RIGHT_7_IC_1_VALUE        0x0

/* SPDIF_RX_PB_RIGHT_8  - Registers (IC 1) */
#define REG_SPDIF_RX_PB_RIGHT_8_IC_1_ADDR         0xF688
#define REG_SPDIF_RX_PB_RIGHT_8_IC_1_BYTE         0
#define REG_SPDIF_RX_PB_RIGHT_8_IC_1_VALUE        0x0

/* SPDIF_RX_PB_RIGHT_9  - Registers (IC 1) */
#define REG_SPDIF_RX_PB_RIGHT_9_IC_1_ADDR         0xF689
#define REG_SPDIF_RX_PB_RIGHT_9_IC_1_BYTE         0
#define REG_SPDIF_RX_PB_RIGHT_9_IC_1_VALUE        0xB

/* SPDIF_RX_PB_RIGHT_10  - Registers (IC 1) */
#define REG_SPDIF_RX_PB_RIGHT_10_IC_1_ADDR        0xF68A
#define REG_SPDIF_RX_PB_RIGHT_10_IC_1_BYTE        0
#define REG_SPDIF_RX_PB_RIGHT_10_IC_1_VALUE       0x220

/* SPDIF_RX_PB_RIGHT_11  - Registers (IC 1) */
#define REG_SPDIF_RX_PB_RIGHT_11_IC_1_ADDR        0xF68B
#define REG_SPDIF_RX_PB_RIGHT_11_IC_1_BYTE        0
#define REG_SPDIF_RX_PB_RIGHT_11_IC_1_VALUE       0x7A04

/* SPDIF_TX_EN  - Registers (IC 1) */
#define REG_SPDIF_TX_EN_IC_1_ADDR                 0xF690
#define REG_SPDIF_TX_EN_IC_1_BYTE                 2
#define REG_SPDIF_TX_EN_IC_1_VALUE                0x1

/* SPDIF_TX_CTRL  - Registers (IC 1) */
#define REG_SPDIF_TX_CTRL_IC_1_ADDR               0xF691
#define REG_SPDIF_TX_CTRL_IC_1_BYTE               2
#define REG_SPDIF_TX_CTRL_IC_1_VALUE              0x0

/* SPDIF_TX_AUXBIT_SOURCE  - Registers (IC 1) */
#define REG_SPDIF_TX_AUXBIT_SOURCE_IC_1_ADDR      0xF69F
#define REG_SPDIF_TX_AUXBIT_SOURCE_IC_1_BYTE      2
#define REG_SPDIF_TX_AUXBIT_SOURCE_IC_1_VALUE     0x0

/* SPDIF_TX_CS_LEFT_0  - Registers (IC 1) */
#define REG_SPDIF_TX_CS_LEFT_0_IC_1_ADDR          0xF6A0
#define REG_SPDIF_TX_CS_LEFT_0_IC_1_BYTE          2
#define REG_SPDIF_TX_CS_LEFT_0_IC_1_VALUE         0x0

/* SPDIF_TX_CS_LEFT_1  - Registers (IC 1) */
#define REG_SPDIF_TX_CS_LEFT_1_IC_1_ADDR          0xF6A1
#define REG_SPDIF_TX_CS_LEFT_1_IC_1_BYTE          2
#define REG_SPDIF_TX_CS_LEFT_1_IC_1_VALUE         0x0

/* SPDIF_TX_CS_LEFT_2  - Registers (IC 1) */
#define REG_SPDIF_TX_CS_LEFT_2_IC_1_ADDR          0xF6A2
#define REG_SPDIF_TX_CS_LEFT_2_IC_1_BYTE          2
#define REG_SPDIF_TX_CS_LEFT_2_IC_1_VALUE         0x0

/* SPDIF_TX_CS_LEFT_3  - Registers (IC 1) */
#define REG_SPDIF_TX_CS_LEFT_3_IC_1_ADDR          0xF6A3
#define REG_SPDIF_TX_CS_LEFT_3_IC_1_BYTE          2
#define REG_SPDIF_TX_CS_LEFT_3_IC_1_VALUE         0x0

/* SPDIF_TX_CS_LEFT_4  - Registers (IC 1) */
#define REG_SPDIF_TX_CS_LEFT_4_IC_1_ADDR          0xF6A4
#define REG_SPDIF_TX_CS_LEFT_4_IC_1_BYTE          2
#define REG_SPDIF_TX_CS_LEFT_4_IC_1_VALUE         0x0

/* SPDIF_TX_CS_LEFT_5  - Registers (IC 1) */
#define REG_SPDIF_TX_CS_LEFT_5_IC_1_ADDR          0xF6A5
#define REG_SPDIF_TX_CS_LEFT_5_IC_1_BYTE          2
#define REG_SPDIF_TX_CS_LEFT_5_IC_1_VALUE         0x0

/* SPDIF_TX_CS_LEFT_6  - Registers (IC 1) */
#define REG_SPDIF_TX_CS_LEFT_6_IC_1_ADDR          0xF6A6
#define REG_SPDIF_TX_CS_LEFT_6_IC_1_BYTE          2
#define REG_SPDIF_TX_CS_LEFT_6_IC_1_VALUE         0x0

/* SPDIF_TX_CS_LEFT_7  - Registers (IC 1) */
#define REG_SPDIF_TX_CS_LEFT_7_IC_1_ADDR          0xF6A7
#define REG_SPDIF_TX_CS_LEFT_7_IC_1_BYTE          2
#define REG_SPDIF_TX_CS_LEFT_7_IC_1_VALUE         0x0

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
#define REG_BCLK_IN1_PIN_IC_1_VALUE               0x18

/* BCLK_IN2_PIN  - Registers (IC 1) */
#define REG_BCLK_IN2_PIN_IC_1_ADDR                0xF782
#define REG_BCLK_IN2_PIN_IC_1_BYTE                2
#define REG_BCLK_IN2_PIN_IC_1_VALUE               0x18

/* BCLK_IN3_PIN  - Registers (IC 1) */
#define REG_BCLK_IN3_PIN_IC_1_ADDR                0xF783
#define REG_BCLK_IN3_PIN_IC_1_BYTE                2
#define REG_BCLK_IN3_PIN_IC_1_VALUE               0x18

/* BCLK_OUT0_PIN  - Registers (IC 1) */
#define REG_BCLK_OUT0_PIN_IC_1_ADDR               0xF784
#define REG_BCLK_OUT0_PIN_IC_1_BYTE               2
#define REG_BCLK_OUT0_PIN_IC_1_VALUE              0x18

/* BCLK_OUT1_PIN  - Registers (IC 1) */
#define REG_BCLK_OUT1_PIN_IC_1_ADDR               0xF785
#define REG_BCLK_OUT1_PIN_IC_1_BYTE               2
#define REG_BCLK_OUT1_PIN_IC_1_VALUE              0x18

/* BCLK_OUT2_PIN  - Registers (IC 1) */
#define REG_BCLK_OUT2_PIN_IC_1_ADDR               0xF786
#define REG_BCLK_OUT2_PIN_IC_1_BYTE               2
#define REG_BCLK_OUT2_PIN_IC_1_VALUE              0x18

/* BCLK_OUT3_PIN  - Registers (IC 1) */
#define REG_BCLK_OUT3_PIN_IC_1_ADDR               0xF787
#define REG_BCLK_OUT3_PIN_IC_1_BYTE               2
#define REG_BCLK_OUT3_PIN_IC_1_VALUE              0x18

/* LRCLK_IN0_PIN  - Registers (IC 1) */
#define REG_LRCLK_IN0_PIN_IC_1_ADDR               0xF788
#define REG_LRCLK_IN0_PIN_IC_1_BYTE               2
#define REG_LRCLK_IN0_PIN_IC_1_VALUE              0x18

/* LRCLK_IN1_PIN  - Registers (IC 1) */
#define REG_LRCLK_IN1_PIN_IC_1_ADDR               0xF789
#define REG_LRCLK_IN1_PIN_IC_1_BYTE               2
#define REG_LRCLK_IN1_PIN_IC_1_VALUE              0x18

/* LRCLK_IN2_PIN  - Registers (IC 1) */
#define REG_LRCLK_IN2_PIN_IC_1_ADDR               0xF78A
#define REG_LRCLK_IN2_PIN_IC_1_BYTE               2
#define REG_LRCLK_IN2_PIN_IC_1_VALUE              0x18

/* LRCLK_IN3_PIN  - Registers (IC 1) */
#define REG_LRCLK_IN3_PIN_IC_1_ADDR               0xF78B
#define REG_LRCLK_IN3_PIN_IC_1_BYTE               2
#define REG_LRCLK_IN3_PIN_IC_1_VALUE              0x18

/* LRCLK_OUT0_PIN  - Registers (IC 1) */
#define REG_LRCLK_OUT0_PIN_IC_1_ADDR              0xF78C
#define REG_LRCLK_OUT0_PIN_IC_1_BYTE              2
#define REG_LRCLK_OUT0_PIN_IC_1_VALUE             0x18

/* LRCLK_OUT1_PIN  - Registers (IC 1) */
#define REG_LRCLK_OUT1_PIN_IC_1_ADDR              0xF78D
#define REG_LRCLK_OUT1_PIN_IC_1_BYTE              2
#define REG_LRCLK_OUT1_PIN_IC_1_VALUE             0x18

/* LRCLK_OUT2_PIN  - Registers (IC 1) */
#define REG_LRCLK_OUT2_PIN_IC_1_ADDR              0xF78E
#define REG_LRCLK_OUT2_PIN_IC_1_BYTE              2
#define REG_LRCLK_OUT2_PIN_IC_1_VALUE             0x18

/* LRCLK_OUT3_PIN  - Registers (IC 1) */
#define REG_LRCLK_OUT3_PIN_IC_1_ADDR              0xF78F
#define REG_LRCLK_OUT3_PIN_IC_1_BYTE              2
#define REG_LRCLK_OUT3_PIN_IC_1_VALUE             0x18

/* SDATA_IN0_PIN  - Registers (IC 1) */
#define REG_SDATA_IN0_PIN_IC_1_ADDR               0xF790
#define REG_SDATA_IN0_PIN_IC_1_BYTE               2
#define REG_SDATA_IN0_PIN_IC_1_VALUE              0x18

/* SDATA_IN1_PIN  - Registers (IC 1) */
#define REG_SDATA_IN1_PIN_IC_1_ADDR               0xF791
#define REG_SDATA_IN1_PIN_IC_1_BYTE               2
#define REG_SDATA_IN1_PIN_IC_1_VALUE              0x18

/* SDATA_IN2_PIN  - Registers (IC 1) */
#define REG_SDATA_IN2_PIN_IC_1_ADDR               0xF792
#define REG_SDATA_IN2_PIN_IC_1_BYTE               2
#define REG_SDATA_IN2_PIN_IC_1_VALUE              0x18

/* SDATA_IN3_PIN  - Registers (IC 1) */
#define REG_SDATA_IN3_PIN_IC_1_ADDR               0xF793
#define REG_SDATA_IN3_PIN_IC_1_BYTE               2
#define REG_SDATA_IN3_PIN_IC_1_VALUE              0x18

/* SDATA_OUT0_PIN  - Registers (IC 1) */
#define REG_SDATA_OUT0_PIN_IC_1_ADDR              0xF794
#define REG_SDATA_OUT0_PIN_IC_1_BYTE              2
#define REG_SDATA_OUT0_PIN_IC_1_VALUE             0x8

/* SDATA_OUT1_PIN  - Registers (IC 1) */
#define REG_SDATA_OUT1_PIN_IC_1_ADDR              0xF795
#define REG_SDATA_OUT1_PIN_IC_1_BYTE              2
#define REG_SDATA_OUT1_PIN_IC_1_VALUE             0x8

/* SDATA_OUT2_PIN  - Registers (IC 1) */
#define REG_SDATA_OUT2_PIN_IC_1_ADDR              0xF796
#define REG_SDATA_OUT2_PIN_IC_1_BYTE              2
#define REG_SDATA_OUT2_PIN_IC_1_VALUE             0x8

/* SDATA_OUT3_PIN  - Registers (IC 1) */
#define REG_SDATA_OUT3_PIN_IC_1_ADDR              0xF797
#define REG_SDATA_OUT3_PIN_IC_1_BYTE              2
#define REG_SDATA_OUT3_PIN_IC_1_VALUE             0x8

/* SPDIF_TX_PIN  - Registers (IC 1) */
#define REG_SPDIF_TX_PIN_IC_1_ADDR                0xF798
#define REG_SPDIF_TX_PIN_IC_1_BYTE                2
#define REG_SPDIF_TX_PIN_IC_1_VALUE               0x8

/* SCLK_SCL_PIN  - Registers (IC 1) */
#define REG_SCLK_SCL_PIN_IC_1_ADDR                0xF799
#define REG_SCLK_SCL_PIN_IC_1_BYTE                2
#define REG_SCLK_SCL_PIN_IC_1_VALUE               0x8

/* MISO_SDA_PIN  - Registers (IC 1) */
#define REG_MISO_SDA_PIN_IC_1_ADDR                0xF79A
#define REG_MISO_SDA_PIN_IC_1_BYTE                2
#define REG_MISO_SDA_PIN_IC_1_VALUE               0x8

/* SS_PIN  - Registers (IC 1) */
#define REG_SS_PIN_IC_1_ADDR                      0xF79B
#define REG_SS_PIN_IC_1_BYTE                      2
#define REG_SS_PIN_IC_1_VALUE                     0x18

/* MOSI_ADDR1_PIN  - Registers (IC 1) */
#define REG_MOSI_ADDR1_PIN_IC_1_ADDR              0xF79C
#define REG_MOSI_ADDR1_PIN_IC_1_BYTE              2
#define REG_MOSI_ADDR1_PIN_IC_1_VALUE             0x18

/* SCLK_SCL_M_PIN  - Registers (IC 1) */
#define REG_SCLK_SCL_M_PIN_IC_1_ADDR              0xF79D
#define REG_SCLK_SCL_M_PIN_IC_1_BYTE              2
#define REG_SCLK_SCL_M_PIN_IC_1_VALUE             0xF

/* MISO_SDA_M_PIN  - Registers (IC 1) */
#define REG_MISO_SDA_M_PIN_IC_1_ADDR              0xF79E
#define REG_MISO_SDA_M_PIN_IC_1_BYTE              2
#define REG_MISO_SDA_M_PIN_IC_1_VALUE             0xF

/* SS_M_PIN  - Registers (IC 1) */
#define REG_SS_M_PIN_IC_1_ADDR                    0xF79F
#define REG_SS_M_PIN_IC_1_BYTE                    2
#define REG_SS_M_PIN_IC_1_VALUE                   0xF

/* MOSI_M_PIN  - Registers (IC 1) */
#define REG_MOSI_M_PIN_IC_1_ADDR                  0xF7A0
#define REG_MOSI_M_PIN_IC_1_BYTE                  2
#define REG_MOSI_M_PIN_IC_1_VALUE                 0xF

/* MP6_PIN  - Registers (IC 1) */
#define REG_MP6_PIN_IC_1_ADDR                     0xF7A1
#define REG_MP6_PIN_IC_1_BYTE                     2
#define REG_MP6_PIN_IC_1_VALUE                    0x18

/* MP7_PIN  - Registers (IC 1) */
#define REG_MP7_PIN_IC_1_ADDR                     0xF7A2
#define REG_MP7_PIN_IC_1_BYTE                     2
#define REG_MP7_PIN_IC_1_VALUE                    0x18

/* CLKOUT_PIN  - Registers (IC 1) */
#define REG_CLKOUT_PIN_IC_1_ADDR                  0xF7A3
#define REG_CLKOUT_PIN_IC_1_BYTE                  2
#define REG_CLKOUT_PIN_IC_1_VALUE                 0x8

/* SOFT_RESET  - Registers (IC 1) */
#define REG_SOFT_RESET_IC_1_ADDR                  0xF890
#define REG_SOFT_RESET_IC_1_BYTE                  2
#define REG_SOFT_RESET_IC_1_VALUE                 0x1


/*
 *
 * Control register's field descriptions
 *
 */

/* PLL_CTRL0 (IC 1) */
#define R0_PLL_CTRL0_PLL_FBDIVIDER_IC_1           0x60   /* 1100000b	[6:0] */
#define R0_PLL_CTRL0_PLL_FBDIVIDER_IC_1_MASK      0x7F
#define R0_PLL_CTRL0_PLL_FBDIVIDER_IC_1_SHIFT     0

/* PLL_CTRL1 (IC 1) */
#define R1_PLL_CTRL1_PLL_DIV_IC_1                 0x3    /* 11b	[1:0] */
#define R1_PLL_CTRL1_PLL_DIV_IC_1_MASK            0x3
#define R1_PLL_CTRL1_PLL_DIV_IC_1_SHIFT           0

/* PLL_CLK_SRC (IC 1) */
#define R2_PLL_CLK_SRC_CLKSRC_IC_1                0x1    /* 1b	[0] */
#define R2_PLL_CLK_SRC_CLKSRC_IC_1_MASK           0x1
#define R2_PLL_CLK_SRC_CLKSRC_IC_1_SHIFT          0

/* PLL_ENABLE (IC 1) */
#define R3_PLL_ENABLE_PLL_ENABLE_IC_1             0x1    /* 1b	[0] */
#define R3_PLL_ENABLE_PLL_ENABLE_IC_1_MASK        0x1
#define R3_PLL_ENABLE_PLL_ENABLE_IC_1_SHIFT       0

/* PLL_LOCK (IC 1) */
#define R4_PLL_LOCK_PLL_LOCK_IC_1                 0x1    /* 1b	[0] */
#define R4_PLL_LOCK_PLL_LOCK_IC_1_MASK            0x1
#define R4_PLL_LOCK_PLL_LOCK_IC_1_SHIFT           0

/* MCLK_OUT (IC 1) */
#define R5_MCLK_OUT_CLKOUT_ENABLE_IC_1            0x1    /* 1b	[0] */
#define R5_MCLK_OUT_CLKOUT_RATE_IC_1              0x3    /* 11b	[2:1] */
#define R5_MCLK_OUT_CLKOUT_ENABLE_IC_1_MASK       0x1
#define R5_MCLK_OUT_CLKOUT_ENABLE_IC_1_SHIFT      0
#define R5_MCLK_OUT_CLKOUT_RATE_IC_1_MASK         0x6
#define R5_MCLK_OUT_CLKOUT_RATE_IC_1_SHIFT        1

/* PLL_WATCHDOG (IC 1) */
#define R6_PLL_WATCHDOG_PLL_WATCHDOG_IC_1         0x1    /* 1b	[0] */
#define R6_PLL_WATCHDOG_PLL_WATCHDOG_IC_1_MASK    0x1
#define R6_PLL_WATCHDOG_PLL_WATCHDOG_IC_1_SHIFT   0

/* CLK_GEN1_M (IC 1) */
#define R7_CLK_GEN1_M_CLOCKGEN1_M_IC_1            0x06   /* 000000110b	[8:0] */
#define R7_CLK_GEN1_M_CLOCKGEN1_M_IC_1_MASK       0x1FF
#define R7_CLK_GEN1_M_CLOCKGEN1_M_IC_1_SHIFT      0

/* CLK_GEN1_N (IC 1) */
#define R8_CLK_GEN1_N_CLOCKGEN1_N_IC_1            0x01   /* 000000001b	[8:0] */
#define R8_CLK_GEN1_N_CLOCKGEN1_N_IC_1_MASK       0x1FF
#define R8_CLK_GEN1_N_CLOCKGEN1_N_IC_1_SHIFT      0

/* CLK_GEN2_M (IC 1) */
#define R9_CLK_GEN2_M_CLOCKGEN2_M_IC_1            0x09   /* 000001001b	[8:0] */
#define R9_CLK_GEN2_M_CLOCKGEN2_M_IC_1_MASK       0x1FF
#define R9_CLK_GEN2_M_CLOCKGEN2_M_IC_1_SHIFT      0

/* CLK_GEN2_N (IC 1) */
#define R10_CLK_GEN2_N_CLOCKGEN2_N_IC_1           0x01   /* 000000001b	[8:0] */
#define R10_CLK_GEN2_N_CLOCKGEN2_N_IC_1_MASK      0x1FF
#define R10_CLK_GEN2_N_CLOCKGEN2_N_IC_1_SHIFT     0

/* CLK_GEN3_M (IC 1) */
#define R11_CLK_GEN3_M_CLOCKGEN3_M_IC_1           0x0000 /* 0000000000000000b	[15:0] */
#define R11_CLK_GEN3_M_CLOCKGEN3_M_IC_1_MASK      0xFFFF
#define R11_CLK_GEN3_M_CLOCKGEN3_M_IC_1_SHIFT     0

/* CLK_GEN3_N (IC 1) */
#define R12_CLK_GEN3_N_CLOCKGEN3_N_IC_1           0x0000 /* 0000000000000000b	[15:0] */
#define R12_CLK_GEN3_N_CLOCKGEN3_N_IC_1_MASK      0xFFFF
#define R12_CLK_GEN3_N_CLOCKGEN3_N_IC_1_SHIFT     0

/* CLK_GEN3_SRC (IC 1) */
#define R13_CLK_GEN3_SRC_FREF_PIN_IC_1            0xE    /* 1110b	[3:0] */
#define R13_CLK_GEN3_SRC_CLK_GEN3_SRC_IC_1        0x0    /* 0b	[4] */
#define R13_CLK_GEN3_SRC_FREF_PIN_IC_1_MASK       0xF
#define R13_CLK_GEN3_SRC_FREF_PIN_IC_1_SHIFT      0
#define R13_CLK_GEN3_SRC_CLK_GEN3_SRC_IC_1_MASK   0x10
#define R13_CLK_GEN3_SRC_CLK_GEN3_SRC_IC_1_SHIFT  4

/* CLK_GEN3_LOCK (IC 1) */
#define R14_CLK_GEN3_LOCK_GEN3_LOCK_IC_1          0x1    /* 1b	[0] */
#define R14_CLK_GEN3_LOCK_GEN3_LOCK_IC_1_MASK     0x1
#define R14_CLK_GEN3_LOCK_GEN3_LOCK_IC_1_SHIFT    0

/* POWER_ENABLE0 (IC 1) */
#define R15_POWER_ENABLE0_SIN0_PWR_IC_1           0x1    /* 1b	[0] */
#define R15_POWER_ENABLE0_SIN1_PWR_IC_1           0x1    /* 1b	[1] */
#define R15_POWER_ENABLE0_SIN2_PWR_IC_1           0x1    /* 1b	[2] */
#define R15_POWER_ENABLE0_SIN3_PWR_IC_1           0x1    /* 1b	[3] */
#define R15_POWER_ENABLE0_SOUT0_PWR_IC_1          0x1    /* 1b	[4] */
#define R15_POWER_ENABLE0_SOUT1_PWR_IC_1          0x1    /* 1b	[5] */
#define R15_POWER_ENABLE0_SOUT2_PWR_IC_1          0x1    /* 1b	[6] */
#define R15_POWER_ENABLE0_SOUT3_PWR_IC_1          0x1    /* 1b	[7] */
#define R15_POWER_ENABLE0_ASRCBANK0_PWR_IC_1      0x1    /* 1b	[8] */
#define R15_POWER_ENABLE0_ASRCBANK1_PWR_IC_1      0x0    /* 0b	[9] */
#define R15_POWER_ENABLE0_CLK_GEN1_PWR_IC_1       0x1    /* 1b	[10] */
#define R15_POWER_ENABLE0_CLK_GEN2_PWR_IC_1       0x0    /* 0b	[11] */
#define R15_POWER_ENABLE0_CLK_GEN3_PWR_IC_1       0x0    /* 0b	[12] */
#define R15_POWER_ENABLE0_SIN0_PWR_IC_1_MASK      0x1
#define R15_POWER_ENABLE0_SIN0_PWR_IC_1_SHIFT     0
#define R15_POWER_ENABLE0_SIN1_PWR_IC_1_MASK      0x2
#define R15_POWER_ENABLE0_SIN1_PWR_IC_1_SHIFT     1
#define R15_POWER_ENABLE0_SIN2_PWR_IC_1_MASK      0x4
#define R15_POWER_ENABLE0_SIN2_PWR_IC_1_SHIFT     2
#define R15_POWER_ENABLE0_SIN3_PWR_IC_1_MASK      0x8
#define R15_POWER_ENABLE0_SIN3_PWR_IC_1_SHIFT     3
#define R15_POWER_ENABLE0_SOUT0_PWR_IC_1_MASK     0x10
#define R15_POWER_ENABLE0_SOUT0_PWR_IC_1_SHIFT    4
#define R15_POWER_ENABLE0_SOUT1_PWR_IC_1_MASK     0x20
#define R15_POWER_ENABLE0_SOUT1_PWR_IC_1_SHIFT    5
#define R15_POWER_ENABLE0_SOUT2_PWR_IC_1_MASK     0x40
#define R15_POWER_ENABLE0_SOUT2_PWR_IC_1_SHIFT    6
#define R15_POWER_ENABLE0_SOUT3_PWR_IC_1_MASK     0x80
#define R15_POWER_ENABLE0_SOUT3_PWR_IC_1_SHIFT    7
#define R15_POWER_ENABLE0_ASRCBANK0_PWR_IC_1_MASK 0x100
#define R15_POWER_ENABLE0_ASRCBANK0_PWR_IC_1_SHIFT 8
#define R15_POWER_ENABLE0_ASRCBANK1_PWR_IC_1_MASK 0x200
#define R15_POWER_ENABLE0_ASRCBANK1_PWR_IC_1_SHIFT 9
#define R15_POWER_ENABLE0_CLK_GEN1_PWR_IC_1_MASK  0x400
#define R15_POWER_ENABLE0_CLK_GEN1_PWR_IC_1_SHIFT 10
#define R15_POWER_ENABLE0_CLK_GEN2_PWR_IC_1_MASK  0x800
#define R15_POWER_ENABLE0_CLK_GEN2_PWR_IC_1_SHIFT 11
#define R15_POWER_ENABLE0_CLK_GEN3_PWR_IC_1_MASK  0x1000
#define R15_POWER_ENABLE0_CLK_GEN3_PWR_IC_1_SHIFT 12

/* POWER_ENABLE1 (IC 1) */
#define R16_POWER_ENABLE1_ADC_PWR_IC_1            0x1    /* 1b	[0] */
#define R16_POWER_ENABLE1_RX_PWR_IC_1             0x1    /* 1b	[1] */
#define R16_POWER_ENABLE1_TX_PWR_IC_1             0x1    /* 1b	[2] */
#define R16_POWER_ENABLE1_PDM0_PWR_IC_1           0x0    /* 0b	[3] */
#define R16_POWER_ENABLE1_PDM1_PWR_IC_1           0x0    /* 0b	[4] */
#define R16_POWER_ENABLE1_ADC_PWR_IC_1_MASK       0x1
#define R16_POWER_ENABLE1_ADC_PWR_IC_1_SHIFT      0
#define R16_POWER_ENABLE1_RX_PWR_IC_1_MASK        0x2
#define R16_POWER_ENABLE1_RX_PWR_IC_1_SHIFT       1
#define R16_POWER_ENABLE1_TX_PWR_IC_1_MASK        0x4
#define R16_POWER_ENABLE1_TX_PWR_IC_1_SHIFT       2
#define R16_POWER_ENABLE1_PDM0_PWR_IC_1_MASK      0x8
#define R16_POWER_ENABLE1_PDM0_PWR_IC_1_SHIFT     3
#define R16_POWER_ENABLE1_PDM1_PWR_IC_1_MASK      0x10
#define R16_POWER_ENABLE1_PDM1_PWR_IC_1_SHIFT     4

/* ASRC_INPUT0 (IC 1) */
#define R17_ASRC_INPUT0_ASRC_SOURCE_IC_1          0x3    /* 011b	[2:0] */
#define R17_ASRC_INPUT0_ASRC_SIN_CHANNEL_IC_1     0x0    /* 00000b	[7:3] */
#define R17_ASRC_INPUT0_ASRC_SOURCE_IC_1_MASK     0x7
#define R17_ASRC_INPUT0_ASRC_SOURCE_IC_1_SHIFT    0
#define R17_ASRC_INPUT0_ASRC_SIN_CHANNEL_IC_1_MASK 0xF8
#define R17_ASRC_INPUT0_ASRC_SIN_CHANNEL_IC_1_SHIFT 3

/* ASRC_INPUT1 (IC 1) */
#define R18_ASRC_INPUT1_ASRC_SOURCE_IC_1          0x0    /* 000b	[2:0] */
#define R18_ASRC_INPUT1_ASRC_SIN_CHANNEL_IC_1     0x0    /* 00000b	[7:3] */
#define R18_ASRC_INPUT1_ASRC_SOURCE_IC_1_MASK     0x7
#define R18_ASRC_INPUT1_ASRC_SOURCE_IC_1_SHIFT    0
#define R18_ASRC_INPUT1_ASRC_SIN_CHANNEL_IC_1_MASK 0xF8
#define R18_ASRC_INPUT1_ASRC_SIN_CHANNEL_IC_1_SHIFT 3

/* ASRC_INPUT2 (IC 1) */
#define R19_ASRC_INPUT2_ASRC_SOURCE_IC_1          0x0    /* 000b	[2:0] */
#define R19_ASRC_INPUT2_ASRC_SIN_CHANNEL_IC_1     0x0    /* 00000b	[7:3] */
#define R19_ASRC_INPUT2_ASRC_SOURCE_IC_1_MASK     0x7
#define R19_ASRC_INPUT2_ASRC_SOURCE_IC_1_SHIFT    0
#define R19_ASRC_INPUT2_ASRC_SIN_CHANNEL_IC_1_MASK 0xF8
#define R19_ASRC_INPUT2_ASRC_SIN_CHANNEL_IC_1_SHIFT 3

/* ASRC_INPUT3 (IC 1) */
#define R20_ASRC_INPUT3_ASRC_SOURCE_IC_1          0x0    /* 000b	[2:0] */
#define R20_ASRC_INPUT3_ASRC_SIN_CHANNEL_IC_1     0x0    /* 00000b	[7:3] */
#define R20_ASRC_INPUT3_ASRC_SOURCE_IC_1_MASK     0x7
#define R20_ASRC_INPUT3_ASRC_SOURCE_IC_1_SHIFT    0
#define R20_ASRC_INPUT3_ASRC_SIN_CHANNEL_IC_1_MASK 0xF8
#define R20_ASRC_INPUT3_ASRC_SIN_CHANNEL_IC_1_SHIFT 3

/* ASRC_INPUT4 (IC 1) */
#define R21_ASRC_INPUT4_ASRC_SOURCE_IC_1          0x0    /* 000b	[2:0] */
#define R21_ASRC_INPUT4_ASRC_SIN_CHANNEL_IC_1     0x0    /* 00000b	[7:3] */
#define R21_ASRC_INPUT4_ASRC_SOURCE_IC_1_MASK     0x7
#define R21_ASRC_INPUT4_ASRC_SOURCE_IC_1_SHIFT    0
#define R21_ASRC_INPUT4_ASRC_SIN_CHANNEL_IC_1_MASK 0xF8
#define R21_ASRC_INPUT4_ASRC_SIN_CHANNEL_IC_1_SHIFT 3
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
