freeDSP/freeDSP-aurora/SOURCES/WEBAPP/ESP32/aurora/web.cpp

#include <Arduino.h>
#include <WiFi.h>
#include <ESPAsyncWebServer.h>
#include <AsyncJson.h>
#include <SPIFFS.h>
#include <Update.h>
#include <ArduinoJson.h>

#include "plugin.h"
#include "web.h"
#include "webota.h"
#include "fallback.h"
#include "adau1452.h"
#include "AK4458.h"
#include "AK5558.h"
#include "settings.h"
#include "addons.h"
#include "display.h"
#include "channelnames.h"
#include "inputrouting.h"
#include "hwconfig.h"
#include "plugin.h"
#include "inputrouting.h"

#if HAVE_DISPLAY
extern void updateUI(void);
extern Display myDisplay;
#endif

extern String sourceNames[kNumSourceNames];

AsyncWebServer server( 80 );
uint8_t currentFirUploadIdx = 0;
File fileUpload;

//==============================================================================
/*! Converts a uint32 to a hex string with leading 0x
 *
 * \param uintval Value to be converted
 * \return Hex string
 */
String uinttohexstring( uint32_t uintval )
{
  String str = String(F("0x"));
  for( int ii = 0; ii < 4; ii++ )
  {
    uint8_t val = (uintval>>(24-ii*8)) & 0xFF;
    if( val < 0x10 )
      str = str + String(F("0")) + String( val, HEX );
    else
      str = str + String( val, HEX );
  }
  return str;
}


//==============================================================================
/*! Handles the GET request for Input selection
 *
 */
void handleGetInputJson( AsyncWebServerRequest* request )
{
  #if DEBUG_PRINT
  Serial.println(F("GET /input"));
  #endif

  AsyncJsonResponse* response = new AsyncJsonResponse();

  JsonVariant& jsonResponse = response->getRoot();
  jsonResponse["chn0"] = paramInputs[0].sel;
  jsonResponse["chn1"] = paramInputs[1].sel;
  jsonResponse["chn2"] = paramInputs[2].sel;
  jsonResponse["chn3"] = paramInputs[3].sel;
  jsonResponse["chn4"] = paramInputs[4].sel;
  jsonResponse["chn5"] = paramInputs[5].sel;
  jsonResponse["chn6"] = paramInputs[6].sel;
  jsonResponse["chn7"] = paramInputs[7].sel;

  response->setLength();
  request->send(response);
}

//==============================================================================
/*! Handles the GET request for High Pass parameter
 *
 */
void handleGetHpJson( AsyncWebServerRequest* request )
{
  #if DEBUG_PRINT
  Serial.println(F("GET /hp"));
  #endif

  AsyncJsonResponse* response = new AsyncJsonResponse();

  if( request->hasParam( "idx" ) )
  {
    AsyncWebParameter* idx = request->getParam(0);
    int offset = idx->value().toInt();
    JsonVariant& jsonResponse = response->getRoot();
    jsonResponse["typ"] = paramHP[offset].typ;
    jsonResponse["fc"] = paramHP[offset].fc;
    if( paramHP[offset].bypass )
      jsonResponse["bypass"] = String( "1" );
    else
      jsonResponse["bypass"] = String( "0" );
  }
  else
    Serial.println(F("[ERROR] handleGetHpJson(): No id param"));

  response->setLength();
  request->send(response);
}

//==============================================================================
/*! Handles the GET request for Low Shelving parameter
 *
 */
void handleGetLshelvJson( AsyncWebServerRequest* request )
{
  #if DEBUG_PRINT
  Serial.println(F("GET /lshelv"));
  #endif

  AsyncJsonResponse* response = new AsyncJsonResponse();

  if( request->hasParam( "idx" ) )
  {
    AsyncWebParameter* idx = request->getParam(0);
    int offset = idx->value().toInt();
    JsonVariant& jsonResponse = response->getRoot();
    jsonResponse["gain"] = paramLshelv[offset].gain;
    jsonResponse["fc"] = paramLshelv[offset].fc;
    jsonResponse["slope"] = paramLshelv[offset].slope;
    if( paramLshelv[offset].bypass )
      jsonResponse["bypass"] = String( "1" );
    else
      jsonResponse["bypass"] = String( "0" );
  }
  else
    Serial.println(F("[ERROR] handleGetLshelvJson(): No id param"));

  response->setLength();
  request->send(response);
}

//==============================================================================
/*! Handles the GET request for PEQ parameter
 *
 */
void handleGetPeqJson( AsyncWebServerRequest* request )
{
  #if DEBUG_PRINT
  Serial.println(F("GET /peq"));
  #endif

  AsyncJsonResponse* response = new AsyncJsonResponse();

  if(request->hasParam("idx"))
  {
    AsyncWebParameter* idx = request->getParam(0);
    int offset = idx->value().toInt();
    JsonVariant& jsonResponse = response->getRoot();
    jsonResponse["gain"] = paramPeq[offset].gain;
    jsonResponse["fc"] = paramPeq[offset].fc;
    jsonResponse["Q"] = paramPeq[offset].Q;
    if( paramPeq[offset].bypass )
      jsonResponse["bypass"] = String(F("1"));
    else
      jsonResponse["bypass"] = String(F("0"));
  }
  else
    Serial.println(F("[ERROR] handleGetPeqJson(): No id param"));

  response->setLength();
  request->send(response);
}

//==============================================================================
/*! Handles the GET request for PeqBank parameter
 *
 */
void handleGetPeqBankJson( AsyncWebServerRequest* request )
{
  #if DEBUG_PRINT
  Serial.println(F("GET /peqbank"));
  #endif

  if(request->hasParam("idx"))
  {
    AsyncWebParameter* idx = request->getParam(0);
    int offset = idx->value().toInt();
    int numBands = paramPeqBank[offset].numBands;

    // Build the JSON response manually. Via ArduinoJson it did not work somehow.
    String array("{");
    if(paramPeqBank[offset].numBands > 0)
    {
      array += String(F("\"fc\":["));
      for(int ii = 0; ii < numBands - 1; ii++)
        array += String(F("\"")) + String(paramPeqBank[offset].fc[ii]) + String(F("\","));
      array += String(F("\"")) + String(paramPeqBank[offset].fc[numBands - 1]);
      array += String(F("\"],"));

      array += String(F("\"Q\":["));
      for(int ii = 0; ii < numBands - 1; ii++)
        array += String(F("\"")) + String(paramPeqBank[offset].Q[ii]) + String(F("\","));
      array += String(F("\"")) + String(paramPeqBank[offset].Q[numBands - 1]);
      array += String(F("\"],"));

      array += String(F("\"V0\":["));
      for(int ii = 0; ii < numBands - 1; ii++)
        array += String(F("\"")) + String(paramPeqBank[offset].gain[ii]) + String(F("\","));
      array += String(F("\"")) + String(paramPeqBank[offset].gain[numBands - 1]);
      array += String(F("\"],"));

      array += String(F("\"bypass\":["));
      for(int ii = 0; ii < numBands - 1; ii++)
      {
        if(paramPeqBank[offset].bypass[ii])
          array += String(F("\"1\","));
        else
          array += String(F("\"0\","));
      }
      if(paramPeqBank[offset].bypass[numBands - 1])
        array += String(F("\"1\""));
      else
        array += String(F("\"0\""));
      array += String(F("]"));
    }
    array += String("}");
    request->send(200, F("text/plain"), array);
  }
  else
  {
    Serial.println(F("[ERROR] handleGetPeqBankJson(): No id param"));
    request->send(400, F("text/plain"), F("Error params"));
  }
}

//==============================================================================
/*! Handles the GET request for High Shelving parameter
 *
 */
void handleGetHshelvJson( AsyncWebServerRequest* request )
{
  #if DEBUG_PRINT
  Serial.println(F("GET /hshelv"));
  #endif

  AsyncJsonResponse* response = new AsyncJsonResponse();

  if(request->hasParam("idx"))
  {
    AsyncWebParameter* idx = request->getParam(0);
    int offset = idx->value().toInt();
    JsonVariant& jsonResponse = response->getRoot();
    jsonResponse["gain"] = paramHshelv[offset].gain;
    jsonResponse["fc"] = paramHshelv[offset].fc;
    jsonResponse["slope"] = paramHshelv[offset].slope;
    if( paramHshelv[offset].bypass )
      jsonResponse["bypass"] = String( "1" );
    else
      jsonResponse["bypass"] = String( "0" );
  }
  else
    Serial.println(F("[ERROR] handleGetHshelvJson(): No id param"));

  response->setLength();
  request->send(response);
}

//==============================================================================
/*! Handles the GET request for Low Pass parameter
 *
 */
void handleGetLpJson( AsyncWebServerRequest* request )
{
  #if DEBUG_PRINT
  Serial.println(F("GET /lp"));
  #endif

  AsyncJsonResponse* response = new AsyncJsonResponse();

  if(request->hasParam("idx"))
  {
    AsyncWebParameter* idx = request->getParam(0);
    int offset = idx->value().toInt();
    JsonVariant& jsonResponse = response->getRoot();
    jsonResponse["typ"] = paramLP[offset].typ;
    jsonResponse["fc"] = paramLP[offset].fc;
    if( paramLP[offset].bypass )
      jsonResponse["bypass"] = String( "1" );
    else
      jsonResponse["bypass"] = String( "0" );
  }
  else
    Serial.println(F("[ERROR] handleGetLpJson(): No id param"));

  response->setLength();
  request->send(response);
}

//==============================================================================
/*! Handles the GET request for Allpass parameter
 *
 */
void handleGetPhaseJson( AsyncWebServerRequest* request )
{
  #if DEBUG_PRINT
  Serial.println(F("GET /phase"));
  #endif

  AsyncJsonResponse* response = new AsyncJsonResponse();

  if(request->hasParam("idx"))
  {
    AsyncWebParameter* idx = request->getParam(0);
    int offset = idx->value().toInt();
    JsonVariant& jsonResponse = response->getRoot();
    jsonResponse["Q"] = paramPhase[offset].Q;
    jsonResponse["fc"] = paramPhase[offset].fc;
    if( paramPhase[offset].inv )
      jsonResponse["inv"] = String(F("1"));
    else
      jsonResponse["inv"] = String(F("0"));

    if( paramPhase[offset].bypass )
      jsonResponse["bypass"] = String(F("1"));
    else
      jsonResponse["bypass"] = String(F("0"));
  }
  else
    Serial.println(F("[ERROR] handleGetPhaseJson(): No id param"));

  response->setLength();
  request->send(response);
}

//==============================================================================
/*! Handles the GET request for Delay parameter
 *
 */
void handleGetDelayJson( AsyncWebServerRequest* request )
{
  #if DEBUG_PRINT
  Serial.println(F("GET /delay"));
  #endif

  AsyncJsonResponse* response = new AsyncJsonResponse();

  if(request->hasParam("idx"))
  {
    AsyncWebParameter* idx = request->getParam(0);
    int offset = idx->value().toInt();
    JsonVariant& jsonResponse = response->getRoot();
    jsonResponse["dly"] = paramDelay[offset].delay;
    if( paramDelay[offset].bypass )
      jsonResponse["bypass"] = String(F("1"));
    else
      jsonResponse["bypass"] = String(F("0"));
  }
  else
    Serial.println(F("[ERROR] handleGetDelayJson(): No id param"));

  response->setLength();
  request->send(response);
}

//==============================================================================
/*! Handles the GET request for Gain parameter
 *
 */
void handleGetGainJson( AsyncWebServerRequest* request )
{
  #if DEBUG_PRINT
  Serial.println(F("GET /gain"));
  #endif

  AsyncJsonResponse* response = new AsyncJsonResponse();

  if(request->hasParam("idx"))
  {
    AsyncWebParameter* idx = request->getParam(0);
    int offset = idx->value().toInt();
    JsonVariant& jsonResponse = response->getRoot();
    jsonResponse["gain"] = paramGain[offset].gain;
    if( paramGain[offset].mute == true )
      jsonResponse["mute"] = String(F("1"));
    else
      jsonResponse["mute"] = String(F("0"));
  }
  else
    Serial.println(F("[ERROR] handleGetGainJson(): No id param"));

  response->setLength();
  request->send(response);
}

//==============================================================================
/*! Handles the GET request for crossover parameters
 *
 */
void handleGetXoJson( AsyncWebServerRequest* request )
{
  #if DEBUG_PRINT
  Serial.println(F("GET /xo"));
  #endif

  AsyncJsonResponse* response = new AsyncJsonResponse();

  if(request->hasParam("idx"))
  {
    AsyncWebParameter* idx = request->getParam(0);
    int offset = idx->value().toInt();
    JsonVariant& jsonResponse = response->getRoot();
    jsonResponse["lp_typ"] = paramCrossover[offset].lp_typ;
    jsonResponse["lp_fc"] = paramCrossover[offset].lp_fc;
    if( paramCrossover[offset].lp_bypass )
      jsonResponse["lp_bypass"] = String(F("1"));
    else
      jsonResponse["lp_bypass"] = String(F("0"));
    jsonResponse["hp_typ"] = paramCrossover[offset].hp_typ;
    jsonResponse["hp_fc"] = paramCrossover[offset].hp_fc;
    if( paramCrossover[offset].hp_bypass )
      jsonResponse["hp_bypass"] = String(F("1"));
    else
      jsonResponse["hp_bypass"] = String(F("0"));
  }
  else
    Serial.println(F("[ERROR] handleGetXoJson(): No id param"));

  response->setLength();
  request->send(response);
}

//==============================================================================
/*! Handles the GET request for a FIR impulse response
 *
 */
void handleGetFirJson( AsyncWebServerRequest* request )
{
  #if DEBUG_PRINT
  Serial.println(F("GET /fir"));
  #endif

  AsyncJsonResponse* response = new AsyncJsonResponse();

  if(request->hasParam("idx"))
  {
    AsyncWebParameter* idx = request->getParam(0);
    int offset = idx->value().toInt();
    JsonVariant& jsonResponse = response->getRoot();

    if( paramFir[offset].bypass )
      jsonResponse["bypass"] = String(F("1"));
    else
      jsonResponse["bypass"] = String(F("0"));
  }
  else
    Serial.println(F("[ERROR] handleGetFirJson(): No id param"));

  response->setLength();
  request->send(response);
}

//==============================================================================
/*! Handles the GET request for Master Volume parameter
 *
 */
void handleGetMasterVolumeJson( AsyncWebServerRequest* request )
{
  #if DEBUG_PRINT
  Serial.println(F("GET /mvol"));
  #endif
  AsyncJsonResponse* response = new AsyncJsonResponse();
  JsonVariant& jsonResponse = response->getRoot();
  jsonResponse["vol"] = masterVolume.val;
  response->setLength();
  request->send(response);
}

//==============================================================================
/*! Handles the GET request for Preset selection
 *
 */
void handleGetPresetJson( AsyncWebServerRequest* request )
{
  #if DEBUG_PRINT
  Serial.println(F("GET /preset"));
  #endif
  AsyncJsonResponse* response = new AsyncJsonResponse();
  JsonVariant& jsonResponse = response->getRoot();
  jsonResponse["pre"] = currentPreset;
  response->setLength();
  request->send(response);
}

//==============================================================================
/*! Handles the GET request for device configuration
 *
 */
void handleGetConfigJson( AsyncWebServerRequest* request )
{
  #if DEBUG_PRINT
  Serial.println(F("GET /config"));
  #endif
  AsyncJsonResponse* response = new AsyncJsonResponse();
  JsonVariant& jsonResponse = response->getRoot();

  jsonResponse["aid"] = Settings.addonid;
  jsonResponse["vpot"] = Settings.vpot;
  jsonResponse["fw"] = VERSION_STR;
  jsonResponse["plugin"] = pluginVersion; 
  jsonResponse["ip"] = WiFi.localIP().toString();
  jsonResponse["pre"] = currentPreset;

  if( Settings.addonid == ADDON_B )
  {
    jsonResponse["addcfg"] = currentAddOnCfg[2];
  }
  else
    jsonResponse["addcfg"] = 0;

  jsonResponse["adcsum"] = Settings.adcsum;

  if(currentPlugInName == String(F("stereoforever")) || currentPlugInName == String(F("The Room")))
    jsonResponse["vinputs"] = true;
  else
    jsonResponse["vinputs"] = false;

  response->setLength();
  request->send(response);
}

//==============================================================================
/*! Handles the GET request for device configuration
 *
 */
void handleGetAddonConfigJson( AsyncWebServerRequest* request )
{
  #if DEBUG_PRINT
  Serial.println(F("GET /addoncfg"));
  #endif

  AsyncJsonResponse* response = new AsyncJsonResponse();
  JsonVariant& jsonResponse = response->getRoot();

  if( Settings.addonid == ADDON_B )
  {
    jsonResponse["addcfg"] = currentAddOnCfg[2];
  }
  else
    jsonResponse["addcfg"] = 0;

  response->setLength();
  request->send(response);
}

//==============================================================================
/*! Handles the GET request for bypass status of all dsp blocks
 *
 */
String handleGetAllBypJson( void )
{
  #if DEBUG_PRINT
  Serial.println(F("GET /allbyp"));
  #endif

  // Build the JSON response manually. Via ArduinoJson it did not work somehow.
  String array( "{\"byp\":[" );
  for( int ii = 0; ii < numHPs; ii++ )
  {
    array += String("{\"name\":\"hp") + String(ii) + String("\",\"val\":");

    if( paramHP[ii].bypass )
      array += String( "1}" );
    else
      array += String( "0}" );

    array += String( "," );
  }
  for( int ii = 0; ii < numLShelvs; ii++ )
  {
    array += String("{\"name\":\"ls") + String(ii) + String("\",\"val\":");

    if( paramLshelv[ii].bypass )
      array += String( "1}" );
    else
      array += String( "0}" );

    array += String( "," );
  }
  for( int ii = 0; ii < numPeqBanks; ii++ )
  {
    array += String("{\"name\":\"peqbank") + String(ii) + String("\",\"val\":");
    bool haveBypass = false;

    for(int nn = 0; nn < paramPeqBank[ii].numBands; nn++)
    {
      if(paramPeqBank[ii].bypass[nn])
        haveBypass = true;
    }

    if(haveBypass)
      array += String( "1}" );
    else
      array += String( "0}" );

    array += String( "," );
  }
  for( int ii = 0; ii < numPEQs; ii++ )
  {
    array += String("{\"name\":\"peq") + String(ii) + String("\",\"val\":");

    if( paramPeq[ii].bypass )
      array += String( "1}" );
    else
      array += String( "0}" );

    array += String( "," );
  }
  for( int ii = 0; ii < numHShelvs; ii++ )
  {
    array += String("{\"name\":\"hs") + String(ii) + String("\",\"val\":");

    if( paramHshelv[ii].bypass )
      array += String( "1}" );
    else
      array += String( "0}" );

    array += String( "," );
  }
  for( int ii = 0; ii < numLPs; ii++ )
  {
    array += String("{\"name\":\"lp") + String(ii) + String("\",\"val\":");

    if( paramLP[ii].bypass )
      array += String( "1}" );
    else
      array += String( "0}" );

   array += String( "," );
  }
  for( int ii = 0; ii < numPhases; ii++ )
  {
    array += String("{\"name\":\"ph") + String(ii) + String("\",\"val\":");

    if( paramPhase[ii].bypass )
      array += String( "1}" );
    else
      array += String( "0}" );

    array += String( "," );
  }
  for( int ii = 0; ii < numDelays; ii++ )
  {
    array += String("{\"name\":\"dly") + String(ii) + String("\",\"val\":");

    if( paramDelay[ii].bypass )
      array += String( "1}" );
    else
      array += String( "0}" );

   array += String( "," );
  }
  for( int ii = 0; ii < numGains; ii++ )
  {
    array += String("{\"name\":\"gn") + String(ii) + String("\",\"val\":");

    if( paramGain[ii].mute )
      array += String( "1}" );
    else
      array += String( "0}" );

    array += String( "," );
  }
  for( int ii = 0; ii < numCrossovers; ii++ )
  {
    array += String("{\"name\":\"xo") + String(ii) + String("\",\"val\":");

    if( paramCrossover[ii].lp_bypass || paramCrossover[ii].hp_bypass )
      array += String( "1}" );
    else
      array += String( "0}" );

    array += String( "," );
  }
  for( int ii = 0; ii < numFIRs; ii++ )
  {
    array += String("{\"name\":\"fir") + String(ii) + String("\",\"val\":");

    if( paramFir[ii].bypass )
      array += String( "1}" );
    else
      array += String( "0}" );

    array += String( "," );
  }

  if( array.length() > 1 )
   array = array.substring( 0, array.length()-1 );

  array += String( "]}" );

  return array;
}

//==============================================================================
/*! Handles the GET request for fc of all dsp blocks
 *
 */
String handleGetAllFcJson( void )
{
  #if DEBUG_PRINT
  Serial.println(F("GET /allfc"));
  #endif

  if(!numHPs && !numLShelvs && !numPEQs && !numHShelvs && !numLPs && !numPhases && !numDelays && !numGains)
    return String("{\"fc\":[]}");

  // Build the JSON response manually. Via ArduinoJson it did not work somehow.
  String array( "{\"fc\":[" );
  for( int ii = 0; ii < numHPs; ii++ )
  {
    array += String("{\"name\":\"hp") + String(ii) + String("\",\"val\":");
    if( paramHP[ii].fc < 1000.0 )
      array += String( "\"HP<br><h4>" ) + String( static_cast<int>(paramHP[ii].fc) ) + String( " Hz</h4>\"}" );
    else
    {
      char buf[20];
      dtostrf( paramHP[ii].fc/1000.0 , 1, 1, buf );
      array += String( "\"HP<br><h4>" ) + String( buf ) + String( " kHz</h4>\"}" );
    }
    array += String( "," );
  }
  for( int ii = 0; ii < numLShelvs; ii++ )
  {
    array += String("{\"name\":\"ls") + String(ii) + String("\",\"val\":");
    char buf[20];
    dtostrf( paramLshelv[ii].gain , 1, 1, buf );
    array += String( "\"LShlv<br><h4>" ) + String( buf ) + String( " dB</h4>\"}" );
    array += String( "," );
  }
  for( int ii = 0; ii < numPEQs; ii++ )
  {
    array += String("{\"name\":\"peq") + String(ii) + String("\",\"val\":");
    if( paramPeq[ii].fc < 1000.0 )
      array += String( "\"PEQ<br><h4>" ) + String( static_cast<int>(paramPeq[ii].fc) ) + String( " Hz</h4>\"}" );
    else
    {
      char buf[20];
      dtostrf( paramPeq[ii].fc/1000.0 , 1, 1, buf );
      array += String( "\"PEQ<br><h4>" ) + String( buf ) + String( " kHz</h4>\"}" );
    }
    array += String( "," );
  }
  for( int ii = 0; ii < numHShelvs; ii++ )
  {
    array += String("{\"name\":\"hs") + String(ii) + String("\",\"val\":");
    char buf[20];
    dtostrf( paramHshelv[ii].gain , 1, 1, buf );
    array += String( "\"HShlv<br><h4>" ) + String( buf ) + String( " dB</h4>\"}" );
    array += String( "," );
  }
  for( int ii = 0; ii < numLPs; ii++ )
  {
    array += String("{\"name\":\"lp") + String(ii) + String("\",\"val\":");
    if( paramLP[ii].fc < 1000.0 )
      array += String( "\"LP<br><h4>" ) + String( static_cast<int>(paramLP[ii].fc) ) + String( " Hz</h4>\"}" );
    else
    {
      char buf[20];
      dtostrf( paramLP[ii].fc/1000.0 , 1, 1, buf );
      array += String( "\"LP<br><h4>" ) + String( buf ) + String( " kHz</h4>\"}" );
    }
    array += String( "," );
  }
  for( int ii = 0; ii < numPhases; ii++ )
  {
    array += String("{\"name\":\"ph") + String(ii) + String("\",\"val\":");
    if( paramPhase[ii].fc < 1000.0 )
      array += String( "\"Phase<br><h4>" ) + String( static_cast<int>(paramPhase[ii].fc) ) + String( " Hz</h4>\"}" );
    else
    {
      char buf[20];
      dtostrf( paramPhase[ii].fc/1000.0 , 1, 1, buf );
      array += String( "\"Phase<br><h4>" ) + String( buf ) + String( " kHz</h4>\"}" );
    }
    array += String( "," );
  }
  for( int ii = 0; ii < numDelays; ii++ )
  {
    array += String("{\"name\":\"dly") + String(ii) + String("\",\"val\":");
    char buf[20];
    dtostrf( paramDelay[ii].delay, 1, 1, buf );
    array += String( "\"Delay<br><h4>" ) + String( buf ) + String( " ms</h4>\"}" );
    array += String( "," );
  }
  for( int ii = 0; ii < numGains; ii++ )
  {
    array += String("{\"name\":\"gn") + String(ii) + String("\",\"val\":");
    char buf[20];
    dtostrf( paramGain[ii].gain , 1, 1, buf );
    array += String( "\"Gain<br><h4>" ) + String( buf ) + String( " dB</h4>\"}" );
    array += String( "," );
  }

  if( array.length() > 1 )
   array = array.substring( 0, array.length()-1 );

  array += String( "]}" );

  return array;
}

//==============================================================================
/*! Handles the GET request for all input selections
 *
 */
void handleGetAllInputsJson( AsyncWebServerRequest* request )
{
  #if DEBUG_PRINT
  Serial.println(F("GET /allinputs"));
  #endif

  AsyncJsonResponse* response = new AsyncJsonResponse();
  JsonVariant& jsonResponse = response->getRoot();

  String str;
  uint8_t val;
  String key[] = {"in0", "in1", "in2", "in3", "in4", "in5", "in6", "in7"};

  if(currentPlugInName == String(F("stereoforever")) || currentPlugInName == String(F("The Room")))
    jsonResponse["num"] = 0;
  else
    jsonResponse["num"] = numInputs;

  for( int nn = 0; nn < numInputs; nn++ )
  {
    str = String("0x");
    for( int ii = 0; ii < 4; ii++ )
    {
      val = (paramInputs[nn].sel>>(24-ii*8)) & 0xFF;
      if( val < 0x10 )
        str = str + String( "0") + String( val, HEX );
      else
        str = str + String( val, HEX );
    }
    jsonResponse[key[nn]] = str;
  }

  response->setLength();
  request->send(response);
}

//==============================================================================
/*! Handles the GET request for SPDIF output multiplexer
 *
 */
void handleGetSpdifOutJson( AsyncWebServerRequest* request )
{
  #if DEBUG_PRINT
  Serial.println(F("GET /spdifout"));
  #endif

  AsyncJsonResponse* response = new AsyncJsonResponse();
  JsonVariant& jsonResponse = response->getRoot();

  jsonResponse["spdifleft"] = uinttohexstring( spdifOutput.selectionLeft );
  jsonResponse["spdifright"] = uinttohexstring( spdifOutput.selectionRight );

  response->setLength();
  request->send(response);
}

//==============================================================================
/*! Handles the GET request for access point configuration
 *
 */
void handleGetWifiConfigJson( AsyncWebServerRequest* request )
{
  #if DEBUG_PRINT
  Serial.println(F("GET /wificonfig"));
  #endif

  AsyncJsonResponse* response = new AsyncJsonResponse();
  JsonVariant& jsonResponse = response->getRoot();
  jsonResponse["apname"] = Settings.apname;
  jsonResponse["ssid"] = Settings.ssid;

  response->setLength();
  request->send(response);
}

//==============================================================================
/*! Handles the POST request for Input selection
 *
 */
void handlePostInputJson( AsyncWebServerRequest* request, uint8_t* data )
{
  #if DEBUG_PRINT
  Serial.println(F("POST /input"));
  #endif

  DynamicJsonDocument jsonDoc(1024);
  DeserializationError err = deserializeJson( jsonDoc, (const char*)data );
  if( err )
  {
    Serial.print(F("[ERROR] handlePostHpJson(): Deserialization failed. "));
    Serial.println( err.c_str() );
    request->send( 400, "text/plain", err.c_str() );
    return;
  }

  softMuteDAC();

  JsonObject root = jsonDoc.as<JsonObject>();

  int idx = root["idx"].as<String>().toInt();
  paramInputs[idx].sel = (uint32_t)strtoul( root["sel"].as<String>().c_str(), NULL, 16 );

  setInput( idx );

  request->send(200, "text/plain", "");

  softUnmuteDAC();
}

//==============================================================================
/*! Handles the POST request for High Pass parameter
 *
 */
void handlePostHpJson( AsyncWebServerRequest* request, uint8_t* data )
{
  #if DEBUG_PRINT
  Serial.println(F("POST /hp"));
  #endif

  DynamicJsonDocument jsonDoc(1024);
  DeserializationError err = deserializeJson( jsonDoc, (const char*)data );
  if( err )
  {
    Serial.print(F("[ERROR] handlePostHpJson(): Deserialization failed. "));
    Serial.println( err.c_str() );
    request->send( 400, "text/plain", err.c_str() );
    return;
  }

  softMuteDAC();

  JsonObject root = jsonDoc.as<JsonObject>();

  uint32_t idx = static_cast<uint32_t>(root["idx"].as<String>().toInt());
  paramHP[idx].fc = root["fc"].as<String>().toFloat();
  paramHP[idx].typ = static_cast<tFilterType>(root["typ"].as<String>().toInt());
  if( root["bypass"].as<String>().toInt() == 0 )
    paramHP[idx].bypass = false;
  else
    paramHP[idx].bypass = true;

  setHighPass( idx );

  request->send(200, "text/plain", "");

  softUnmuteDAC();

}

//==============================================================================
/*! Handles the POST request for Low Shelving parameter
 *
 */
void handlePostLshelvJson( AsyncWebServerRequest* request, uint8_t* data )
{
  #if DEBUG_PRINT
  Serial.println(F("POST /lshelv"));
  #endif

  DynamicJsonDocument jsonDoc(1024);
  DeserializationError err = deserializeJson( jsonDoc, (const char*)data );
  if( err )
  {
    Serial.print(F("[ERROR] handlePostHpJson(): Deserialization failed. "));
    Serial.println( err.c_str() );
    request->send( 400, "text/plain", err.c_str() );
    return;
  }

  softMuteDAC();

  JsonObject root = jsonDoc.as<JsonObject>();

  uint32_t idx = static_cast<uint32_t>(root["idx"].as<String>().toInt());
  paramLshelv[idx].gain = root["gain"].as<String>().toFloat();
  paramLshelv[idx].fc = root["fc"].as<String>().toFloat();
  paramLshelv[idx].slope = root["slope"].as<String>().toFloat();
  if( root["bypass"].as<String>().toInt() == 0 )
    paramLshelv[idx].bypass = false;
  else
    paramLshelv[idx].bypass = true;

  setLowShelving( idx );

  request->send(200, "text/plain", "");

  softUnmuteDAC();
}

//==============================================================================
/*! Handles the POST request for PEQ parameter
 *
 */
void handlePostPeqJson( AsyncWebServerRequest* request, uint8_t* data )
{
  #if DEBUG_PRINT
  Serial.println(F("POST /peq"));
  #endif

  DynamicJsonDocument jsonDoc(1024);
  DeserializationError err = deserializeJson( jsonDoc, (const char*)data );
  if( err )
  {
    Serial.print(F("[ERROR] handlePostPeqJson(): Deserialization failed. "));
    Serial.println( err.c_str() );
    request->send( 400, "text/plain", err.c_str() );
    return;
  }

  softMuteDAC();

  JsonObject root = jsonDoc.as<JsonObject>();

  uint32_t idx = static_cast<uint32_t>(root["idx"].as<String>().toInt());
  paramPeq[idx].gain = root["gain"].as<String>().toFloat();
  paramPeq[idx].fc = root["fc"].as<String>().toFloat();
  paramPeq[idx].Q = root["Q"].as<String>().toFloat();
  if( root["bypass"].as<String>().toInt() == 0 )
    paramPeq[idx].bypass = false;
  else
    paramPeq[idx].bypass = true;

  setPEQ( idx );

  request->send(200, "text/plain", "");

  softUnmuteDAC();
}

//==============================================================================
/*! Handles the POST request for Peqbank parameter
 *
 */
void handlePostPeqbankJson( AsyncWebServerRequest* request, uint8_t* data )
{
  #if DEBUG_PRINT
  Serial.println(F("POST /peqbank"));
  #endif

  DynamicJsonDocument jsonDoc(1024);
  DeserializationError err = deserializeJson( jsonDoc, (const char*)data );
  if( err )
  {
    Serial.print(F("[ERROR] handlePostPeqbankJson(): Deserialization failed. "));
    Serial.println(err.c_str());
    request->send(400, "text/plain", err.c_str());
    return;
  }

  softMuteDAC();

  JsonObject root = jsonDoc.as<JsonObject>();

  uint32_t idx = static_cast<uint32_t>(root["idx"].as<String>().toInt());
  paramPeqBank[idx].numBands = static_cast<uint32_t>(root["numbands"].as<String>().toInt());
  for(int nn = 0; nn < paramPeqBank[idx].numBands; nn++)
  {
    paramPeqBank[idx].gain[nn] = root["V0"][nn].as<String>().toFloat();
    paramPeqBank[idx].fc[nn] = root["fc"][nn].as<String>().toFloat();
    paramPeqBank[idx].Q[nn] = root["Q"][nn].as<String>().toFloat();
    if(root["bypass"][nn].as<String>().toInt() == 0)
      paramPeqBank[idx].bypass[nn] = false;
    else
      paramPeqBank[idx].bypass[nn] = true;
  }
  setPeqBank(idx);

  request->send(200, "text/plain", "");

  softUnmuteDAC();
}

//==============================================================================
/*! Handles the POST request for High Shelving parameter
 *
 */
void handlePostHshelvJson( AsyncWebServerRequest* request, uint8_t* data )
{
  #if DEBUG_PRINT
  Serial.println(F("POST /hshelv"));
  #endif

  DynamicJsonDocument jsonDoc(1024);
  DeserializationError err = deserializeJson( jsonDoc, (const char*)data );
  if( err )
  {
    Serial.print(F("[ERROR] handlePostHpJson(): Deserialization failed. "));
    Serial.println( err.c_str() );
    request->send( 400, "text/plain", err.c_str() );
    return;
  }

  softMuteDAC();

  JsonObject root = jsonDoc.as<JsonObject>();

  uint32_t idx = static_cast<uint32_t>(root["idx"].as<String>().toInt());
  paramHshelv[idx].gain = root["gain"].as<String>().toFloat();
  paramHshelv[idx].fc = root["fc"].as<String>().toFloat();
  paramHshelv[idx].slope = root["slope"].as<String>().toFloat();
  if( root["bypass"].as<String>().toInt() == 0 )
    paramHshelv[idx].bypass = false;
  else
    paramHshelv[idx].bypass = true;

  setHighShelving( idx );

  request->send(200, "text/plain", "");

  softUnmuteDAC();
}

//==============================================================================
/*! Handles the POST request for Low Pass parameter
 *
 */
void handlePostLpJson( AsyncWebServerRequest* request, uint8_t* data )
{
  #if DEBUG_PRINT
  Serial.println(F("POST /lp"));
  #endif

  DynamicJsonDocument jsonDoc(1024);
  DeserializationError err = deserializeJson( jsonDoc, (const char*)data );
  if( err )
  {
    Serial.print(F("[ERROR] handlePostLpJson(): Deserialization failed. "));
    Serial.println( err.c_str() );
    request->send( 400, "text/plain", err.c_str() );
    return;
  }

  softMuteDAC();

  JsonObject root = jsonDoc.as<JsonObject>();

  uint32_t idx = static_cast<uint32_t>(root["idx"].as<String>().toInt());
  paramLP[idx].fc = root["fc"].as<String>().toFloat();
  paramLP[idx].typ = static_cast<tFilterType>(root["typ"].as<String>().toInt());
  if( root["bypass"].as<String>().toInt() == 0 )
    paramLP[idx].bypass = false;
  else
    paramLP[idx].bypass = true;

  setLowPass( idx );

  request->send(200, "text/plain", "");

  softUnmuteDAC();
}


//==============================================================================
/*! Handles the POST request for Phase parameter
 *
 */
void handlePostPhaseJson( AsyncWebServerRequest* request, uint8_t* data )
{
  #if DEBUG_PRINT
  Serial.println(F("POST /phase"));
  #endif

  DynamicJsonDocument jsonDoc(1024);
  DeserializationError err = deserializeJson( jsonDoc, (const char*)data );
  if( err )
  {
    Serial.print(F("[ERROR] handlePostPhaseJson(): Deserialization failed. "));
    Serial.println( err.c_str() );
    request->send( 400, "text/plain", err.c_str() );
    return;
  }

  softMuteDAC();

  JsonObject root = jsonDoc.as<JsonObject>();

  uint32_t idx = static_cast<uint32_t>(root["idx"].as<String>().toInt());
  paramPhase[idx].fc = root["fc"].as<String>().toFloat();
  paramPhase[idx].Q = root["Q"].as<String>().toFloat();
  if( root["inv"].as<String>() == "true" )
    paramPhase[idx].inv = true;
  else
    paramPhase[idx].inv = false;

  if( root["bypass"].as<String>().toInt() == 0 )
    paramPhase[idx].bypass = false;
  else
    paramPhase[idx].bypass = true;

  setPhase( idx );

  request->send(200, "text/plain", "");

  softUnmuteDAC();
}

//==============================================================================
/*! Handles the POST request for Delay parameter
 *
 */
void handlePostDelayJson( AsyncWebServerRequest* request, uint8_t* data )
{
  #if DEBUG_PRINT
  Serial.println(F("POST /delay"));
  #endif

  DynamicJsonDocument jsonDoc(1024);
  DeserializationError err = deserializeJson( jsonDoc, (const char*)data );
  if( err )
  {
    Serial.print(F("[ERROR] handlePostDelayJson(): Deserialization failed. "));
    Serial.println( err.c_str() );
    request->send( 400, "text/plain", err.c_str() );
    return;
  }

  softMuteDAC();

  JsonObject root = jsonDoc.as<JsonObject>();
  Serial.println( root["idx"].as<String>() );
  Serial.println( root["delay"].as<String>() );

  uint32_t idx = static_cast<uint32_t>(root["idx"].as<String>().toInt());
  paramDelay[idx].delay = root["delay"].as<String>().toFloat();
  if( root["bypass"].as<String>().toInt() == 0 )
    paramDelay[idx].bypass = false;
  else
    paramDelay[idx].bypass = true;

  setDelay( idx );

  request->send(200, "text/plain", "");

  softUnmuteDAC();
}

//==============================================================================
/*! Handles the POST request for Gain parameter
 *
 */
void handlePostGainJson( AsyncWebServerRequest* request, uint8_t* data )
{
  #if DEBUG_PRINT
  Serial.println(F("POST /gain"));
  #endif

  DynamicJsonDocument jsonDoc(1024);
  DeserializationError err = deserializeJson( jsonDoc, (const char*)data );
  if( err )
  {
    Serial.print(F("[ERROR] handlePostGainJson(): Deserialization failed. "));
    Serial.println( err.c_str() );
    request->send( 400, "text/plain", err.c_str() );
    return;
  }

  softMuteDAC();

  JsonObject root = jsonDoc.as<JsonObject>();

  uint32_t idx = static_cast<uint32_t>(root["idx"].as<String>().toInt());
  paramGain[idx].gain = root["gain"].as<String>().toFloat();
  if( root["mute"].as<String>().toInt() == 0 )
    paramGain[idx].mute = false;
  else
    paramGain[idx].mute = true;

  setGain( idx );

  request->send(200, "text/plain", "");

  softUnmuteDAC();
}

//==============================================================================
/*! Handles the POST request for Low Pass parameter
 *
 */
void handlePostXoJson( AsyncWebServerRequest* request, uint8_t* data )
{
  #if DEBUG_PRINT
  Serial.println(F("POST /xo"));
  #endif

  DynamicJsonDocument jsonDoc(1024);
  DeserializationError err = deserializeJson( jsonDoc, (const char*)data );
  if( err )
  {
    Serial.print(F("[ERROR] handlePostXoJson(): Deserialization failed. "));
    Serial.println( err.c_str() );
    request->send( 400, "text/plain", err.c_str() );
    return;
  }

  softMuteDAC();

  JsonObject root = jsonDoc.as<JsonObject>();
  Serial.println( root["idx"].as<String>() );
  Serial.println( root["lp_fc"].as<String>() );
  Serial.println( root["lp_typ"].as<String>() );
  Serial.println( root["hp_fc"].as<String>() );
  Serial.println( root["hp_typ"].as<String>() );

  uint32_t idx = static_cast<uint32_t>(root["idx"].as<String>().toInt());
  paramCrossover[idx].lp_fc = root["lp_fc"].as<String>().toFloat();
  paramCrossover[idx].lp_typ = static_cast<tFilterType>(root["lp_typ"].as<String>().toInt());
  if( root["lp_bypass"].as<String>().toInt() == 0 )
    paramCrossover[idx].lp_bypass = false;
  else
    paramCrossover[idx].lp_bypass = true;

  paramCrossover[idx].hp_fc = root["hp_fc"].as<String>().toFloat();
  paramCrossover[idx].hp_typ = static_cast<tFilterType>(root["hp_typ"].as<String>().toInt());
  if( root["hp_bypass"].as<String>().toInt() == 0 )
    paramCrossover[idx].hp_bypass = false;
  else
    paramCrossover[idx].hp_bypass = true;

  setCrossover( idx );

  request->send(200, "text/plain", "");

  softUnmuteDAC();
}

//==============================================================================
/*! Handles the POST request for a FIR impulse response
 *
 */
void handlePostFirBypassJson( AsyncWebServerRequest* request, uint8_t* data )
{
  #if DEBUG_PRINT
  Serial.println(F("POST /firbypass"));
  #endif

  DynamicJsonDocument jsonDoc(1024);
  DeserializationError err = deserializeJson( jsonDoc, (const char*)data );
  if( err )
  {
    Serial.print(F("[ERROR] handlePostFirBypassJson(): Deserialization failed. "));
    Serial.println( err.c_str() );
    request->send( 400, "text/plain", err.c_str() );
    return;
  }

  softMuteDAC();

  JsonObject root = jsonDoc.as<JsonObject>();
  Serial.println( root["idx"].as<String>() );

  uint32_t idx = static_cast<uint32_t>(root["idx"].as<String>().toInt());
  if( root["bypass"].as<String>().toInt() == 0 )
    paramFir[idx].bypass = false;
  else
    paramFir[idx].bypass = true;

  if(paramFir[idx].bypass)
    Serial.println("Bypass");

  setFir( idx );

  request->send(200, "text/plain", "");

  softUnmuteDAC();
}

//==============================================================================
/*! Handles the POST request for Master Volume
 *
 */
void handlePostMasterVolumeJson( AsyncWebServerRequest* request, uint8_t* data )
{
  #if DEBUG_PRINT
  Serial.println(F("POST /mvol"));
  #endif

  DynamicJsonDocument jsonDoc(1024);
  DeserializationError err = deserializeJson( jsonDoc, (const char*)data );
  if( err )
  {
    Serial.print(F("[ERROR] handlePostMasterVolumeJson(): Deserialization failed. "));
    Serial.println( err.c_str() );
    request->send( 400, "text/plain", err.c_str() );
    return;
  }

  JsonObject root = jsonDoc.as<JsonObject>();

  masterVolume.val = root["vol"].as<String>().toFloat();

  setMasterVolume();
  updateUI();

  request->send(200, "text/plain", "");
}

//==============================================================================
/*! Handles the POST request for Preset Selection
 *
 */
void handlePostPresetJson( AsyncWebServerRequest* request, uint8_t* data )
{
  #if DEBUG_PRINT
  Serial.println(F("POST /preset"));
  #endif

  if( haveDisplay )
    myDisplay.drawSwitchingPreset();

  DynamicJsonDocument jsonDoc(1024);
  DeserializationError err = deserializeJson( jsonDoc, (const char*)data );
  if( err )
  {
    Serial.print(F("[ERROR] handlePostPresetJson(): Deserialization failed. "));
    Serial.println(err.c_str());
    request->send(400, "text/plain", err.c_str());
    return;
  }

  softMuteDAC();

  JsonObject root = jsonDoc.as<JsonObject>();
  Serial.println( root["pre"].as<String>() );

  currentPreset = root["pre"].as<uint8_t>();

  initUserParams();
  uploadUserParams();

  updateAddOn();

  request->send(200, "text/plain", "");

  updateUI();

  softUnmuteDAC();
}

//==============================================================================
/*! Handles the POST request for device configuration
 *
 */
void handlePostConfigJson( AsyncWebServerRequest* request, uint8_t* data )
{
  #if DEBUG_PRINT
  Serial.println(F("POST /config"));
  #endif

  DynamicJsonDocument jsonDoc(1024);
  DeserializationError err = deserializeJson( jsonDoc, (const char*)data );
  if( err )
  {
    Serial.print(F("[ERROR] handlePostConfigJson(): Deserialization failed. "));
    Serial.println( err.c_str() );
    request->send( 400, "text/plain", err.c_str() );
    return;
  }

  JsonObject root = jsonDoc.as<JsonObject>();

  Settings.addonid = root["aid"].as<String>().toInt();
  if( root["vpot"].as<String>() == "true" )
    Settings.vpot = true;
  else
    Settings.vpot = false;
  Settings.adcsum = root["adcsum"].as<String>().toInt();

  writeSettings();

  enableVolPot();
  changeChannelSummationADC();

  request->send(200, "text/plain", "");
}

//==============================================================================
/*! Handles the POST request for storing current preset
 *
 */
void handlePostStore( AsyncWebServerRequest* request, uint8_t* data )
{
  #if DEBUG_PRINT
  Serial.println(F("POST /store"));
  #endif

  softMuteDAC();

  String fileName = presetUsrparamFile[currentPreset];

  if( SPIFFS.exists( fileName ) )
  {
    if( SPIFFS.remove( fileName ) )
      Serial.println( fileName + " deleted" );
    else
      Serial.println( "[ERROR] Deleting " + fileName );
  }

  Serial.println( "Writing " + fileName );
  File fileUserParams = SPIFFS.open( fileName, "w" );
  if( !fileUserParams )
    Serial.println( "[ERROR] Failed to open " + fileName );
  else
    Serial.println( "Opened " + fileName );

  uint32_t totalSize = 0;
  for( int ii = 0; ii < numInputs; ii++ )
  {
    size_t len = fileUserParams.write( (uint8_t*)&(paramInputs[ii]), sizeof(tInput) );
    if( len != sizeof(tInput) )
      Serial.println( "[ERROR] Writing inputs to " + presetUsrparamFile[currentPreset] );
    totalSize += len;
  }

  for( int ii = 0; ii < numFIRs; ii++ )
  {
    size_t len = fileUserParams.write((uint8_t*)&(paramFir[ii].addr), sizeof(uint16_t));
    len += fileUserParams.write((uint8_t*)&(paramFir[ii].numCoeffs), sizeof(uint16_t));
    len += fileUserParams.write((uint8_t*)&(paramFir[ii].bypass), sizeof(bool));
    if(len != (2 * sizeof(uint16_t) + sizeof(bool)))
      Serial.println( "[ERROR] Writing FIRs to " + presetUsrparamFile[currentPreset] );
    else
    {
      len = fileUserParams.write((uint8_t*)(paramFir[ii].ir), sizeof(float) * paramFir[ii].numCoeffs);
      if(len != sizeof(float) * paramFir[ii].numCoeffs)
        Serial.println( "[ERROR] Reading FIR IR from " + presetUsrparamFile[currentPreset] );
    }
    totalSize += len;
  }

  for( int ii = 0; ii < numHPs; ii++ )
  {
    size_t len = fileUserParams.write( (uint8_t*)&(paramHP[ii]), sizeof(tHPLP) );
    if( len != sizeof(tHPLP) )
      Serial.println( "[ERROR] Writing HPs to " + presetUsrparamFile[currentPreset] );
    totalSize += len;
  }

  for( int ii = 0; ii < numLShelvs; ii++ )
  {
    size_t len = fileUserParams.write( (uint8_t*)&(paramLshelv[ii]), sizeof(tShelving) );
    if( len != sizeof(tShelving) )
      Serial.println( "[ERROR] Writing LShelvs to " + presetUsrparamFile[currentPreset] );
    totalSize += len;
  }

  for( int ii = 0; ii < numPEQs; ii++ )
  {
    size_t len = fileUserParams.write( (uint8_t*)&(paramPeq[ii]), sizeof(tPeq) );
    if( len != sizeof(tPeq) )
      Serial.println( "[ERROR] Writing PEQs to " + presetUsrparamFile[currentPreset] );
    totalSize += len;
  }

  for( int ii = 0; ii < numHShelvs; ii++ )
  {
    size_t len = fileUserParams.write( (uint8_t*)&(paramHshelv[ii]), sizeof(tShelving) );
    if( len != sizeof(tShelving) )
      Serial.println( "[ERROR] Writing HShelvs to " + presetUsrparamFile[currentPreset] );
    totalSize += len;
  }

  for( int ii = 0; ii < numCrossovers; ii++ )
  {
    size_t len = fileUserParams.write( (uint8_t*)&(paramCrossover[ii]), sizeof(tCrossover) );
    if( len != sizeof(tCrossover) )
      Serial.println( "[ERROR] Writing XOs to " + presetUsrparamFile[currentPreset] );
    totalSize += len;
  }

  for( int ii = 0; ii < numLPs; ii++ )
  {
    size_t len = fileUserParams.write( (uint8_t*)&(paramLP[ii]), sizeof(tHPLP) );
    if( len != sizeof(tHPLP) )
      Serial.println( "[ERROR] Writing LPs to " + presetUsrparamFile[currentPreset] );
    totalSize += len;
  }

  for( int ii = 0; ii < numPhases; ii++ )
  {
    size_t len = fileUserParams.write( (uint8_t*)&(paramPhase[ii]), sizeof(tPhase) );
    if( len != sizeof(tPhase) )
      Serial.println( "[ERROR] Writing Phases to " + presetUsrparamFile[currentPreset] );
    totalSize += len;
  }

  for( int ii = 0; ii < numDelays; ii++ )
  {
    size_t len = fileUserParams.write( (uint8_t*)&(paramDelay[ii]), sizeof(tDelay) );
    if( len != sizeof(tDelay) )
      Serial.println( "[ERROR] Writing Delays to " + presetUsrparamFile[currentPreset] );
    totalSize += len;
  }

  for( int ii = 0; ii < numGains; ii++ )
  {
    size_t len = fileUserParams.write( (uint8_t*)&(paramGain[ii]), sizeof(tGain) );
    if( len != sizeof(tGain) )
      Serial.println( "[ERROR] Writing Gains to " + presetUsrparamFile[currentPreset] );
    totalSize += len;
  }

  size_t len = fileUserParams.write( (uint8_t*)&masterVolume, sizeof(tMasterVolume) );
  if( len != sizeof(tMasterVolume) )
    Serial.println( "[ERROR] Writing masterVolume to " + presetUsrparamFile[currentPreset] );
  totalSize += len;

  len = fileUserParams.write( (uint8_t*)&spdifOutput, sizeof(tSpdifOutput) );
  if( len != sizeof(tSpdifOutput) )
    Serial.println( "[ERROR] Writing SPDIF out to " + presetUsrparamFile[currentPreset] );
  totalSize += len;

  for(int ii = 0; ii < numPeqBanks; ii++)
  {
    size_t len = fileUserParams.write((uint8_t*)&(paramPeqBank[ii].numBands), sizeof(uint16_t));
    len += fileUserParams.write((uint8_t*)(paramPeqBank[ii].gain), sizeof(float) * MAX_BANDS_PER_PEQBANK);
    len += fileUserParams.write((uint8_t*)(paramPeqBank[ii].fc), sizeof(float) * MAX_BANDS_PER_PEQBANK);
    len += fileUserParams.write((uint8_t*)(paramPeqBank[ii].Q), sizeof(float) * MAX_BANDS_PER_PEQBANK);
    len += fileUserParams.write((uint8_t*)(paramPeqBank[ii].bypass), sizeof(bool) * MAX_BANDS_PER_PEQBANK);
    if(len != sizeof(uint16_t) + 3 * sizeof(float) * MAX_BANDS_PER_PEQBANK + sizeof(bool) * MAX_BANDS_PER_PEQBANK)
    {  
      Serial.print(F("[ERROR] Writing Peqbank to "));
      Serial.println(presetUsrparamFile[currentPreset]);
    }
    totalSize += len;
  }

  fileUserParams.flush();
  fileUserParams.close();

  Serial.print(F("Wrote "));
  Serial.print( totalSize );
  Serial.println(F("bytes"));

  fileName = presetAddonCfgFile[currentPreset];

  if( SPIFFS.exists( fileName ) )
  {
    if( SPIFFS.remove( fileName ) )
      Serial.println( fileName + " deleted" );
    else
      Serial.println( "[ERROR] Deleting " + fileName );
  }

  Serial.println( "Writing " + fileName );
  File fileAddonConfig = SPIFFS.open( fileName, "w" );
  if( !fileAddonConfig )
    Serial.println( "[ERROR] Failed to open " + fileName );
  else
    Serial.println( "Opened " + fileName );

  totalSize = 0;

  if( Settings.addonid == ADDON_B )
  {
    size_t len = fileAddonConfig.write( currentAddOnCfg, 3 );
    if( len != 3 )
      Serial.println( "[ERROR] Writing AddOn config to " + fileName );
    totalSize += len;
  }

  fileAddonConfig.flush();
  fileAddonConfig.close();

  Serial.print(F("Wrote "));
  Serial.print( totalSize );
  Serial.println(F("bytes"));

  request->send(200, "text/plain", "");

  softUnmuteDAC();
}

//==============================================================================
/*! Handles the POST request for storing addon configuration
 *
 */
void handlePostAddonConfigJson( AsyncWebServerRequest* request, uint8_t* data )
{
  #if DEBUG_PRINT
  Serial.println(F("POST /addoncfg"));
  #endif

  DynamicJsonDocument jsonDoc(1024);
  DeserializationError err = deserializeJson( jsonDoc, (const char*)data );
  if( err )
  {
    Serial.print(F("[ERROR] handlePostAddonConfig(): Deserialization failed. "));
    Serial.println( err.c_str() );
    request->send( 400, "text/plain", err.c_str() );
    return;
  }

  softMuteDAC();

  if( Settings.addonid == ADDON_B )
  {
    JsonObject root = jsonDoc.as<JsonObject>();
    int len = root["len"].as<String>().toInt();
    for( int ii = 0; ii < len; ii++ )
      Serial.println( root["i2c"][ii].as<String>() );

    currentAddOnCfg[0] = (uint8_t)strtoul( root["i2c"][0].as<String>().c_str(), NULL, 16 );
    currentAddOnCfg[1] = (uint8_t)strtoul( root["i2c"][1].as<String>().c_str(), NULL, 16 );
    currentAddOnCfg[2] = (uint8_t)strtoul( root["i2c"][2].as<String>().c_str(), NULL, 16 );

    Wire.beginTransmission( currentAddOnCfg[0]>>1 ); //ADDONB_SPDIFMUX_ADDR
    Wire.write( currentAddOnCfg[1] ); // regaddr
    Wire.write( currentAddOnCfg[2] ); // data
    Wire.endTransmission( true );
  }

  request->send(200, "text/plain", "");

  softUnmuteDAC();
}

//==============================================================================
/*! Handles the POST request for device configuration
 *
 */
void handlePostWifiConfigJson( AsyncWebServerRequest* request, uint8_t* data )
{
  #if DEBUG_PRINT
  Serial.println(F("POST /wifi"));
  #endif

  DynamicJsonDocument jsonDoc(1024);
  DeserializationError err = deserializeJson( jsonDoc, (const char*)data );
  if( err )
  {
    Serial.print(F("[ERROR] handlePostWifiConfigJson(): Deserialization failed. "));
    Serial.println( err.c_str() );
    request->send( 400, "text/plain", err.c_str() );
    return;
  }

  JsonObject root = jsonDoc.as<JsonObject>();

  Settings.ssid = root["ssid"].as<String>();
  Settings.password = root["pwd"].as<String>();

  writeSettings();

  request->send(200, "text/plain", "");
}

//==============================================================================
/*! Handles the POST request for access point password
 *
 */
void handlePostPasswordApJson( AsyncWebServerRequest* request, uint8_t* data )
{
  #if DEBUG_PRINT
  Serial.println(F("POST /pwdap"));
  #endif

  DynamicJsonDocument jsonDoc(1024);
  DeserializationError err = deserializeJson( jsonDoc, (const char*)data );
  if( err )
  {
    Serial.print(F("[ERROR] handlePostPasswordApJson(): Deserialization failed. "));
    Serial.println( err.c_str() );
    request->send( 400, "text/plain", err.c_str() );
    return;
  }

  JsonObject root = jsonDoc.as<JsonObject>();

  Settings.pwdap = root["pwdap"].as<String>();
  Settings.apname = root["apname"].as<String>();

  writeSettings();

  request->send(200, "text/plain", "");
}

//==============================================================================
/*! Handles the POST request for SPDIF output multiplexer
 *
 */
void handlePostSpdifOutJson( AsyncWebServerRequest* request, uint8_t* data )
{
  #if DEBUG_PRINT
  Serial.println(F("POST /spdifout"));
  #endif

  DynamicJsonDocument jsonDoc(1024);
  DeserializationError err = deserializeJson( jsonDoc, (const char*)data );
  if( err )
  {
    Serial.print(F("[ERROR] handlePostConfigJson(): Deserialization failed. "));
    Serial.println( err.c_str() );
    request->send( 400, "text/plain", err.c_str() );
    return;
  }

  JsonObject root = jsonDoc.as<JsonObject>();

  spdifOutput.selectionLeft = (uint32_t)strtoul( root["spdifleft"].as<String>().c_str(), NULL, 16 );
  spdifOutput.selectionRight = (uint32_t)strtoul( root["spdifright"].as<String>().c_str(), NULL, 16 );

  setSpdifOutputRouting();

  request->send(200, "text/plain", "");
}
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
